TexhFexLabs/HydroNodeStation/doc/presentations/Zusatz.pptx

## Autarke IoT-Wetterstation mit LoRaWAN

Seeed Studio XIAO + SX1262 | Helium IoT | HydroNode
IT6 - DAPI

## Slide 2

HydroStation One

Autarke Umweltüberwachung. Intelligent. Vernetzt. Solarbetrieben.

CO₂-Sensor (SCD41)
Photakustisches Prinzip

XIAO ESP32S3

Wio-SX1262 LoRa

LoRa | WiFi | BLE 5.0

Solar Powered

7 Tage
ohne Sonne

LoRaWAN Reichweite
Bis zu 2 km Reichweite
SF7–SF12 Spreading Factor

Temperatur & Luftfeuchte
BME280 Sensor (Bosch)

Helium IoT Netzwerk
Dezentral & permissionless
Globale LoRaWAN-Abdeckung

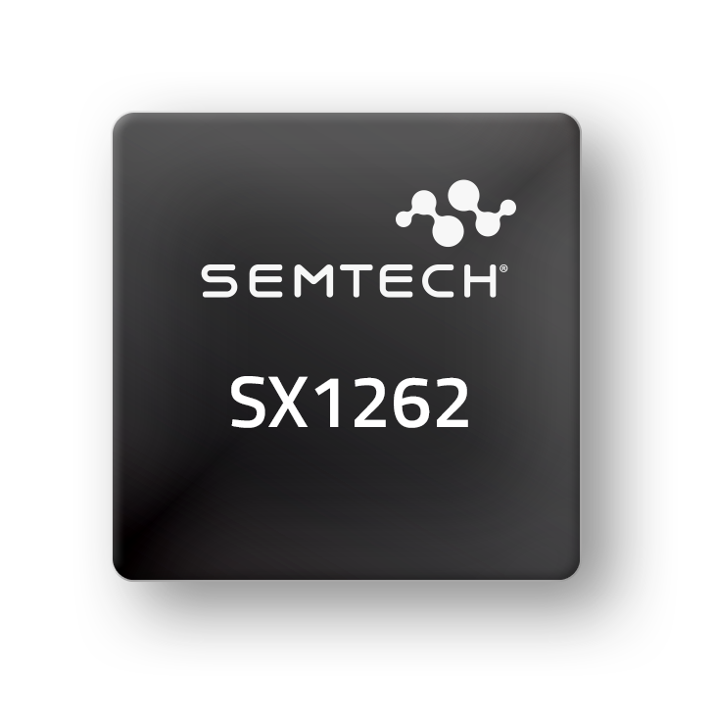
[picture p12: figure]
SX1262

UV-Index Messung
VEML6075
UVA + UVB-Spektrum

7 Tage Autonomie
6W Solarpanel + 2x 3000 mAh LiPo
<2 µA Sleep-Modus

3 Sensoren
integriert

2 km
LoRa Range

1.62 µA
Ultra Low Power

< 100 €
Gesamtsystem

## Slide 3

HydroNode API

Zwei Wege. Eine Plattform. Vollständig abgesichert.

KANAL A

Direkte HTTP-API

IoT-Sensor (ESP32, Arduino)

POST /api/webhook/sensor-value

HMAC-SHA256 Verifikation

Apache Kafka (verified.sensor)

JSON Payload • HTTPS/TLS • ±20 min Replay-Schutz

Header: X-Sensor-Id • X-Timestamp • X-Signature

KANAL B

LoRaWAN / Amazon SNS

LoRaWAN-Sensor

Helium Network / ChirpStack

Amazon SNS (HTTPS)

Apache Kafka (verified.sensor)

Binär-Payload • AES-128 • LoRa Frame Counter

Secret-Hash (SHA-256) • Auto-Subscription

VERARBEITUNG

PostgreSQL
Messwerte speichern

Baseline
72h Rolling Window

Anomalie-Erkennung
Spike • Drop • Drift

GPT-4 Analyse
Alle 60 Minuten
