TexhFexLabs/HydroNodeStation/hardware/schematics_pcb/PCB_PCB2_2026-06-19.pdf

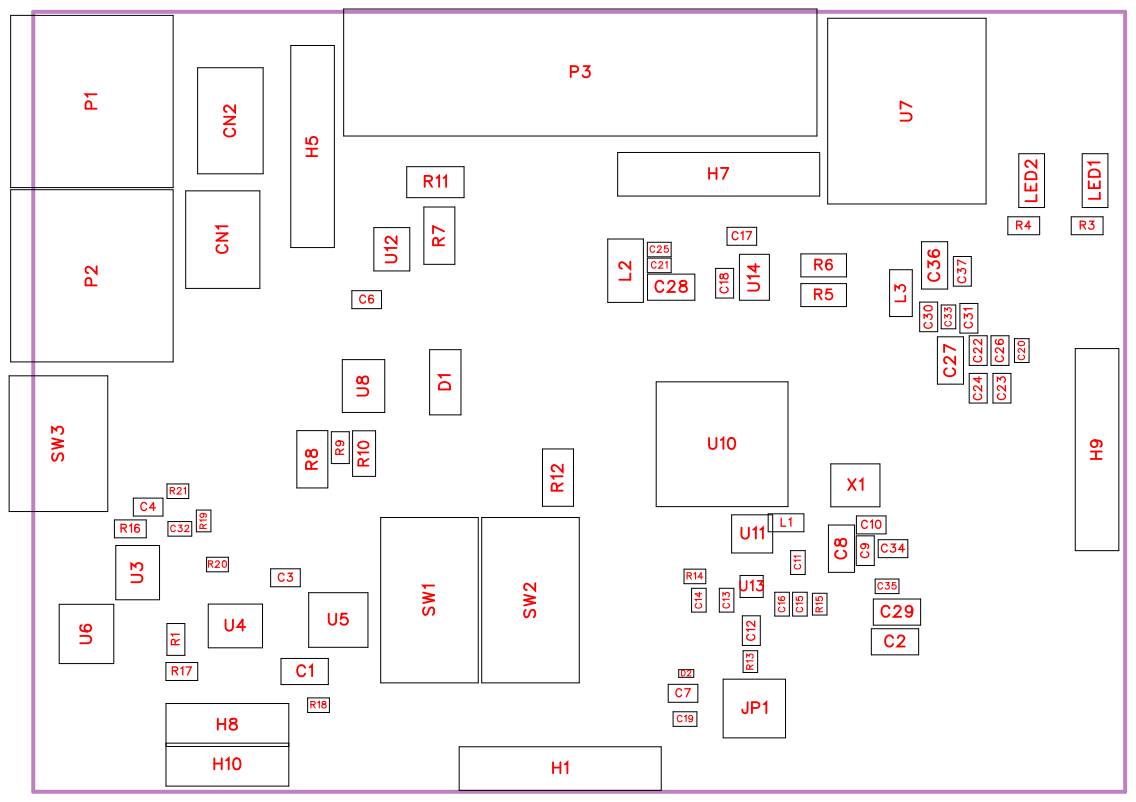
[picture p13: page 1]

No. | Quantity | Comment | Designator | Footprint | Value | Manufacturer Part | Manufacturer | Supplier Part | Supplier | Pin Count | Category
1 | 2 | 22uF | C1,C2 | C0603 | 22uF | CL10A226M Q8NRNC | SAMSUNG( ) 三星 | C59461 | LCSC | 2 | Capacitors:M ultilayer Ceramic Capacitors MLCC -SMD/SMT
2 | 2 | 10uF | C3,C4 | C0402 | 10uF | CL05A106M Q5NUNC | SAMSUNG( 三星 ) | C15525 | LCSC | 2 | Capacitors:M ultilayer Ceramic Capacitors MLCC -SMD/SMT
3 | 10 | 100nF | C6,C7,C22,C23,C24,C26,C 30,C31,C34,C37 | C0402 | 100nF | CC0402KRX 7R7BB104 | YAGEO(国巨 ) | C60474 | LCSC | 2 | Capacitors:M ultilayer Ceramic Capacitors MLCC -SMD/SMT
4 | 1 | 100pF | C8 | C0603 | 100pF | CC0603JRN PO9BN101 | YAGEO(国巨 ) | C14665 | LCSC | 2 | Capacitors:M ultilayer Ceramic Capacitors MLCC -SMD/SMT
5 | 2 | 68pF | C9,C12 | C0402 | 68pF | GCM1555C1 H680JA16D | muRata(村田 ) | C161156 | LCSC | 2 | Capacitors:M ultilayer Ceramic Capacitors MLCC -SMD/SMT
6 | 1 | 47nF | C10 | C0402 | 47nF | GCM155R71 E473KA55D | muRata(村田 ) | C126529 | LCSC | 2 | Capacitors:M ultilayer Ceramic Capacitors MLCC -SMD/SMT
7 | 1 | 68pF | C11 | C0201 | 68pF | GRM0335C1 H680JA01D | muRata(村田 ) | C88914 | LCSC | 2 | Capacitors:M ultilayer Ceramic Capacitors MLCC -SMD/SMT
8 | 3 | 100nF | C13,C15,C19 | C0201 | 100nF | GRM033R61 A104KE15D | muRata(村田 ) | C76934 | LCSC | 2 | Capacitors:M ultilayer Ceramic Capacitors MLCC -SMD/SMT
9 | 2 | 1nF | C14,C16 | C0201 | 1nF | GRM033R71 H102KA12D | muRata(村田 ) | C85934 | LCSC | 2 | Capacitors:M ultilayer Ceramic Capacitors MLCC -SMD/SMT

10 | 2 | 6.8pF | C17,C18 | C0402 | 6.8pF | GJM1555C1 H6R8BB01D | muRata(村田 ) | C88896 | LCSC | 2 | Capacitors:M ultilayer Ceramic Capacitors MLCC -SMD/SMT
11 | 3 | 33pF | C20,C21,C25 | C0201 | 33pF | GJM0335C1 E330GB01D | muRata(村田 ) | C2896796 | LCSC | 2 | Capacitors:M ultilayer Ceramic Capacitors MLCC -SMD/SMT
12 | 3 | 4.7uF | C27,C29,C36 | C0603 | 4.7uF | CC0603KRX 5R7BB475 | YAGEO(国巨 ) | C277476 | LCSC | 2 | Capacitors:M ultilayer Ceramic Capacitors MLCC -SMD/SMT
13 | 1 | 470nF | C28 | C0603 | 470nF | CC0603KRX 5R8BB474 | YAGEO(国巨 ) | C106850 | LCSC | 2 | Capacitors:M ultilayer Ceramic Capacitors MLCC -SMD/SMT
14 | 3 | 100nF | C32,C33,C35 | C0201 | 100nF | C0603X5R1 C104KT00N E | TDK | C694145 | LCSC | 2 | Capacitors:M ultilayer Ceramic Capacitors MLCC -SMD/SMT
15 | 1 | B2B-PH-K-S( LF)(SN) | CN1 | CONN-TH_B 2B-PH-K-S | | B2B-PH-K-S( LF)(SN) | JST | C131337 | LCSC | 2 | Connectors: Wire To Board Connector
16 | 1 | BM04B-SRS S-TB(LF)(SN ) | CN2 | CONN-SMD_ BM04B-SRS S-TB | | BM04B-SRS S-TB(LF)(SN ) | JST | C160390 | LCSC | 6 | Connectors: Wire To Board Connector
17 | 1 | MBRX120LF-TP | D1 | SOD-123_L2 .7-W1.6-LS3. 7-RD | | MBRX120LF-TP | MCC(美微科 ) | C668956 | LCSC | 2 | Diodes:Schot tky Diodes
18 | 1 | ESDALC6V1 -1U2 | D2 | DFN0603-D_ L0.6-W0.3-P 0.34-RD | | ESDALC6V1 -1U2 | ST(意法半导 体) | C1974498 | LCSC | 2 | Circuit Protec tion:ESD and Surge Protection (TVS/ESD)
19 | 4 | PZ254V-11-0 5P | H1,H5,H7,H9 | HDR-TH_5P-P2.54-V-M | | PZ254V-11-0 5P | XFCN(兴飞 ) | C492404 | LCSC | 5 | Connectors:P in Headers
20 | 2 | PZ254V-11-0 3P | H8,H10 | HDR-TH_3P-P2.54-V-M_P Z254V-11-03 P | | PZ254V-11-0 3P | XFCN(兴飞 ) | C2937625 | LCSC | 3 | Connectors:P in Headers

21 | 1 | 6GHz | JP1 | RF-SMD_FR F05002-JSS 103M | 6GHz | U.FL-R-SMT-1(80) | HRS(广濑 ) | C88374 | LCSC | 3 | Connectors: Coaxial Connectors (RF)
22 | 1 | 47nH | L1 | L0402 | 47nH | LQW15AN47 NG00D | muRata(村田 ) | C22334 | LCSC | 2 | Inductors, Coils, Choke s:Power Inductors
23 | 1 | 15uH | L2 | L0805 | 15uH | MLZ2012M1 50WTD25 | TDK | C404760 | LCSC | 2 | Inductors, Coils, Choke s:Inductors (SMD)
24 | 1 | FCM1608KF-601T03 | L3 | L0603 | | FCM1608KF-601T03 | TAI-TECH( 台 庆 ) | C141723 | LCSC | 2 | Filters:Ferrite Beads
25 | 2 | YLED0603R | LED1,LED2 | LED0603-FD | | YLED0603R | YONGYUTAI (永裕泰) | C19171390 | LCSC | 2 | Optoelectroni cs:LED Indication -Discrete
26 | 2 | WJ500V-5.08 -2P | P1,P2 | CONN-TH_2 P-P5.00_WJ 500V-5.08-2 P | | WJ500V-5.08 -2P | KANGNEX( 康奈克斯电气 ) | C8465 | LCSC | 2 | Connectors:S crew Terminal Blocks
27 | 1 | WJ126V-5.0-6P | P3 | CONN-TH_6 P-P5.00_WJ 126V-5.0-6P | | WJ126V-5.0-6P | KANGNEX( 康奈克斯电气 ) | C8379 | LCSC | 6 | Connectors:S crew Terminal Blocks
28 | 2 | 36.5k | R1,R16 | R0402 | 36.5k | 0402WGF36 52TCE | UNI-ROYAL( 厚声 ) | C25887 | LCSC | 2 | Resistors:Chi p Resistor -Surface Mount
29 | 2 | 1k | R3,R4 | R0402 | 1k | FRC0402J10 2 TS | FOJAN(富捷 ) | C2906899 | LCSC | 2 | Resistors:Chi p Resistor -Surface Mount
30 | 2 | 4.7k | R5,R6 | R0603 | 4.7k | 0603WAF47 01T5E | UNI-ROYAL( 厚声 ) | C23162 | LCSC | 2 | Resistors:Chi p Resistor -Surface Mount
31 | 4 | 10k | R7,R8,R11,R12 | R0805 | 10k | FRC0805J10 3TS | FOJAN(富捷 ) | C2930231 | LCSC | 2 | Resistors:Chi p Resistor -Surface Mount
32 | 1 | 12k | R9 | R0402 | 12k | 0402WGF12 02TCE | UNI-ROYAL( 厚声 ) | C25752 | LCSC | 2 | Resistors:Chi p Resistor -Surface Mount
33 | 1 | 300 | R10 | R0603 | 300 | FRC0603J30 1 TS | FOJAN(富捷 ) | C2907148 | LCSC | 2 | Resistors:Chi p Resistor -Surface Mount
34 | 5 | 0 | R13,R18,R19,R20,R21 | R0201 | 0 | CRCW02010 000Z0ED | VISHAY(威世 ) | C844709 | LCSC | 2 | Resistors:Chi p Resistor -Surface Mount

35 | 2 | 100 | R14,R15 | R0201 | 100 | CRCW02011 00RFNED | VISHAY(威世 ) | C2073844 | LCSC | 2 | Resistors:Chi p Resistor -Surface Mount
36 | 1 | 8.25k | R17 | R0402 | 8.25k | FRC0402F82 51TS | FOJAN(富捷 ) | C5126132 | LCSC | 2 | Resistors:Chi p Resistor -Surface Mount
37 | 2 | TS-1095PS-A1B2-C3D2 | SW1,SW2 | KEY-SMD_4 P-L6.0-W6.0-P3.90-LS9.0 | | TS-1095PS-A1B2-C3D2 | Yuandi(元迪 ) | C2834918 | LCSC | 4 | Switches:Tac tile Switches
38 | 1 | MK-12C02-G 020 | SW3 | SW-SMD_M K-12C02-G0 20 | | MK-12C02-G 020 | G-Switch( 品 赞 ) | C963206 | LCSC | 7 | Switches:Slid e Switches
39 | 2 | TPS63900D SKR | U3,U4 | WSON-10_L 2.5-W2.5-W0 .50-TL-EP | | TPS63900D SKR | TI(德州仪器 ) | C1518762 | LCSC | 11 | Power Management (PMIC):DC-D C Converters
40 | 2 | 2.2uH | U5,U6 | IND-SMD_L3 .0-W3.0_LVF 303012-4R7 M-N | 2.2uH | SRN3015-2R 2M | BOURNS | C2041716 | LCSC | 2 | Inductors, Coils, Choke s:Power Inductors
41 | 1 | SMQS-04R-T P | U7 | SW-TH_8P-P 2.54_SMQS-04R-TP | | SMQS-04R-T P | SM Switch | C5299505 | LCSC | 8 | Switches:DIP Switches
42 | 1 | BQ25185DL HR | U8 | WSON-10_L 2.2-W2.0-P0. 40-BL-EP_TI _DLH0010A | | BQ25185DL HR | TI(德州仪器 ) | C19725033 | LCSC | 11 | Power Management (PMIC):Batte ry Management
43 | 1 | STM32WLE5 CCU6 | U10 | UFQFPN-48 _L7.0-W7.0-P0.50-BL-EP 5.6 | | STM32WLE5 CCU6 | ST(意法半导 体) | C2888218 | LCSC | 49 | Embedded Processors & Controllers:M icrocontroller s (MCU/MPU /SOC)
44 | 1 | BALFHB-WL-02D3 | U11 | CSPG-8_L2. 1-W1.8_BAL FHB-WL-03D 3 | | BALFHB-WL-02D3 | ST(意法半导 体) | C5350082 | LCSC | 8 | RF and Wireless:RF Filters
45 | 1 | MAX17048G +T10 | U12 | TDFN-8_L2.0 -W2.0-P0.50-BL-EP1.2 | | MAX17048G +T10 | ADI(亚德诺)/ MAXIM(美信 ) | C2682616 | LCSC | 9 | Power Management (PMIC):Batte ry Management
46 | 1 | BGS12SN6E 6327XTSA1 | U13 | TSNP-6_L1.1 -W0.7-P0.40-BL | | BGS12SN6E 6327XTSA1 | Infineon(英飞 凌) | C114953 | LCSC | 6 | RF and Wireless:RF Switches
47 | 1 | 32.768kHz | U14 | CRYSTAL-S MD_L2.0-W1 .2 | 32.768kHz | NX2012SA-3 2.768KHZ-E XS00A-MU0 0527 | NDK | C7016235 | LCSC | 2 | Crystals, Oscillators, R esonators:Cr ystals

48

1 | 32MHz | X1 | CRYSTAL-S MD_4P-L2.0- W1.6-BL
32MHz | NX2016SA-3
2M-EXS00A-CS06465
NDK | C1986260 | LCSC
4 | Crystals,
Oscillators, R
esonators:Cr
ystals

Add into BOM | Convert to PCB | 3D Model Title | Device | Name
yes | | C0603_L1.6-W0.8-H0.8 | CL10A226M Q8NRNC | 22uF
yes | | C0402_L1.0-W0.5-H0.5 | CL05A106M Q5NUNC | 10uF
yes | | C0402_L1.0-W0.5-H0.5 | CC0402KRX 7R7BB104 | 100nF
yes | | C0603_L1.6-W0.8-H0.8 | CC0603JRN PO9BN101 | 100pF
yes | | C0402_L1.0-W0.5-H0.5 | GCM1555C1 H680JA16D | 68pF
yes | | C0402_L1.0-W0.5-H0.5 | GCM155R71 E473KA55D | 47nF
yes | | C0201_L0.6-W0.3-H0.3 | GRM0335C1 H680JA01D | 68pF
yes | | C0201_L0.6-W0.3-H0.3 | GRM033R61 A104KE15D | 100nF
yes | | C0201_L0.6-W0.3-H0.3 | GRM033R71 H102KA12D | 1nF
yes | | C0402_L1.0-W0.5-H0.5 | GJM1555C1 H6R8BB01D | 6.8pF
yes | | C0201_L0.6-W0.3-H0.3 | GJM0335C1 E330GB01D | 33pF
yes | | C0603_L1.6-W0.8-H0.8 | CC0603KRX 5R7BB475 | 4.7uF
yes | | C0603_L1.6-W0.8-H0.8 | CC0603KRX 5R8BB474 | 470nF
yes | | C0201_L0.6-W0.3-H0.3 | C0603X5R1 C104KT00N E | 100nF
yes | | CONN-TH_P H2.00-LI-2P | B2B-PH-K-S( LF)(SN) | B2B-PH-K-S( LF)(SN)
yes | | CONN-SMD_ 4P-L6.0-W2. 9-H4.3-P1.0 | BM04B-SRS S-TB(LF)(SN ) | BM04B-SRS S-TB(LF)(SN )
yes | | SOD-123_L2 .7-W1.6-H1.4 -LS3.7 | MBRX120LF-TP | MBRX120LF-TP
yes | | DFN0603-D_ L0.6-W0.3-H 0.3 | ESDALC6V1 -1U2 | ESDALC6V1 -1U2
yes | | HDR-TH_5P-P2.54-M-LI-1 X5P | PZ254V-11-0 5P | PZ254V-11-0 5P
yes | | HDR-TH_3P-P2.54-V-M_P Z254V-11-03 P | PZ254V-11-0 3P | PZ254V-11-0 3P

yes | RF-SMD_FR F05002-JSS 103M | U.FL-R-SMT-1(80)_C8837 4 | 6GHz
yes | L0402_L1.0-W0.5-H0.5_B EAD | LQW15AN47 NG00D | 47nH
yes | R0805_L2.0-W1.3-H0.6 | MLZ2012M1 50WTD25 | 15uH
yes | L0603_L1.6-W0.8-H0.5_B EAD | FCM1608KF-601T03 | FCM1608KF-601T03
yes | LED0603_Inf | YLED0603R | YLED0603R
yes | CONN-TH_2 P-P5.00_WJ 500V-5.08-2 P | WJ500V-5.08 -2P | WJ500V-5.08 -2P
yes | CONN-TH_6 P-P5.00_WJ 126V-5.0-6P | WJ126V-5.0-6P | WJ126V-5.0-6P
yes | R0402_L1.0-W0.5-H0.4 | 0402WGF36 52TCE | 36.5k
yes | R0402_L1.0-W0.5-H0.4 | FRC0402J10 2 TS | 1k
yes | R0603 | 0603WAF47 01T5E | 4.7k
yes | R0805_L2.0-W1.3-H0.6 | FRC0805J10 3TS | 10k
yes | R0402_L1.0-W0.5-H0.4 | 0402WGF12 02TCE | 12k
yes | R0603 | FRC0603J30 1 TS | 300
yes | R0201_L0.6-W0.3-H0.3 | CRCW02010 000Z0ED | 0
yes | R0201_L0.6-W0.3-H0.3 | CRCW02011 00RFNED | 100
yes | R0402_L1.0-W0.5-H0.4 | FRC0402F82 51TS | 8.25k
yes | KEY-SMD_4 P-L6.0-W6.0-H8.0-P3.90-L S9.0 | TS-1095PS-A1B2-C3D2 | TS-1095PS-A1B2-C3D2
yes | SW-SMD_M K-12C02-G0 20 | MK-12C02-G 020 | MK-12C02-G 020
yes | WSON-10_L 2.5-W2.5-W0 .50-TL-EP | TPS63900D SKR | TPS63900D SKR
yes | | SRN3015-2R 2M | 2.2uH

yes | SW-TH_8P-P 2.54_SMQS-04R-TP | SMQS-04R-T P | SMQS-04R-T P
yes | WSON-10_L 2.2-W2.0-P0. 40-BL-EP_TI _DLH0010A | BQ25185DL HR | BQ25185DL HR
yes | UFQFPN-48 _L7.0-W7.0-H0.6-P0.50 | STM32WLE5 CCU6 | STM32WLE5 CCU6
yes | CSPG-8_L2. 1-W1.8_BAL FHB-WL-03D 3 | BALFHB-WL-02D3 | BALFHB-WL-02D3
yes | TDFN-8_L2.0 -W2.0-P0.50-BL-EP1.2 | MAX17048G +T10 | MAX17048G +T10
yes | TSNP-6_L1.1 -W0.7-H0.4-P0.40-BL | BGS12SN6E 6327XTSA1 | BGS12SN6E 6327XTSA1
yes | CRYSTAL-S MD_L2.0-W1 .2 | NX2012SA-3 2.768KHZ-E XS00A-MU0 0527 | 32.768kHz
yes | CRYSTAL-S MD_4P-L2.0-W1.6-BL | NX2016SA-3 2M-EXS00A-CS06465 | 32MHz

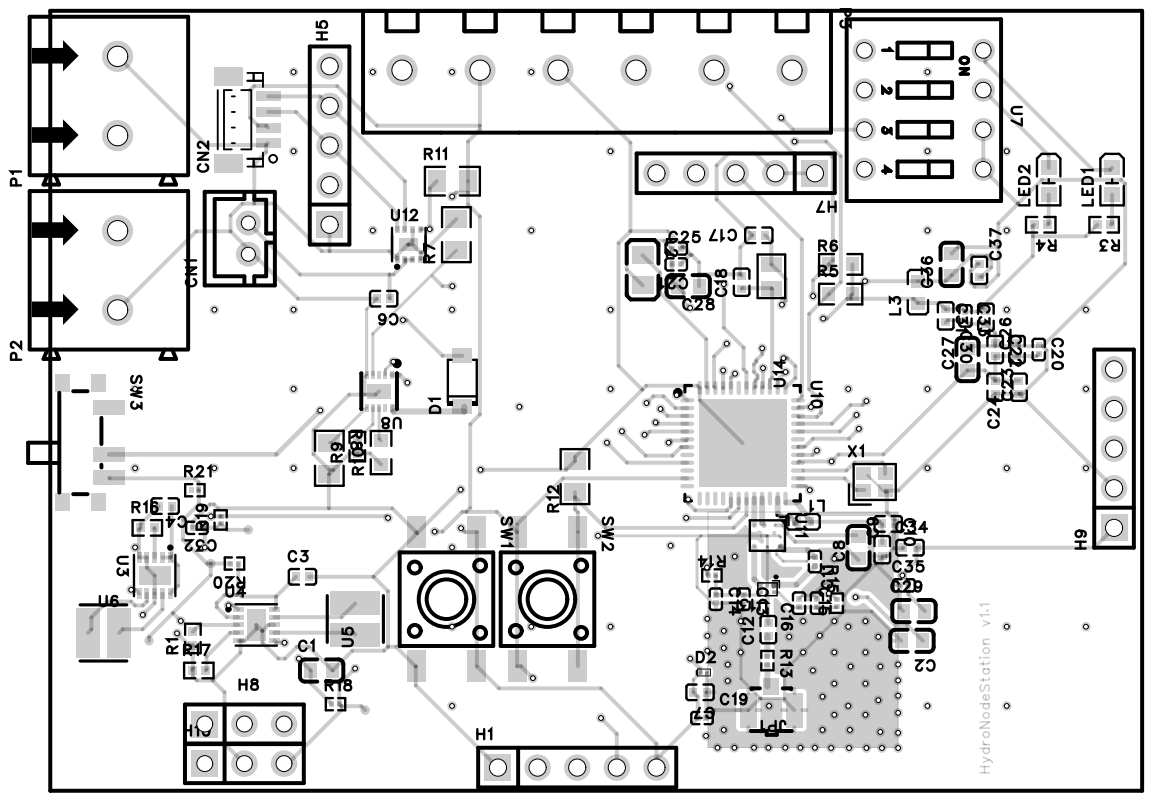
[picture p14: page 11]

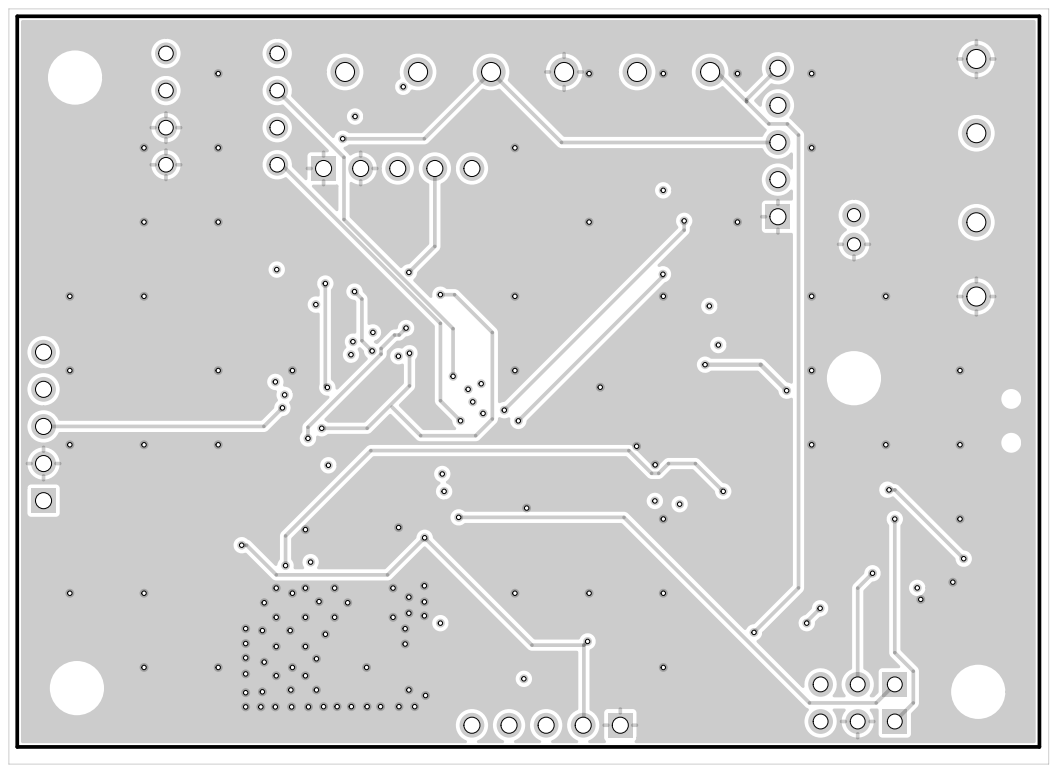
[picture p15: page 12]

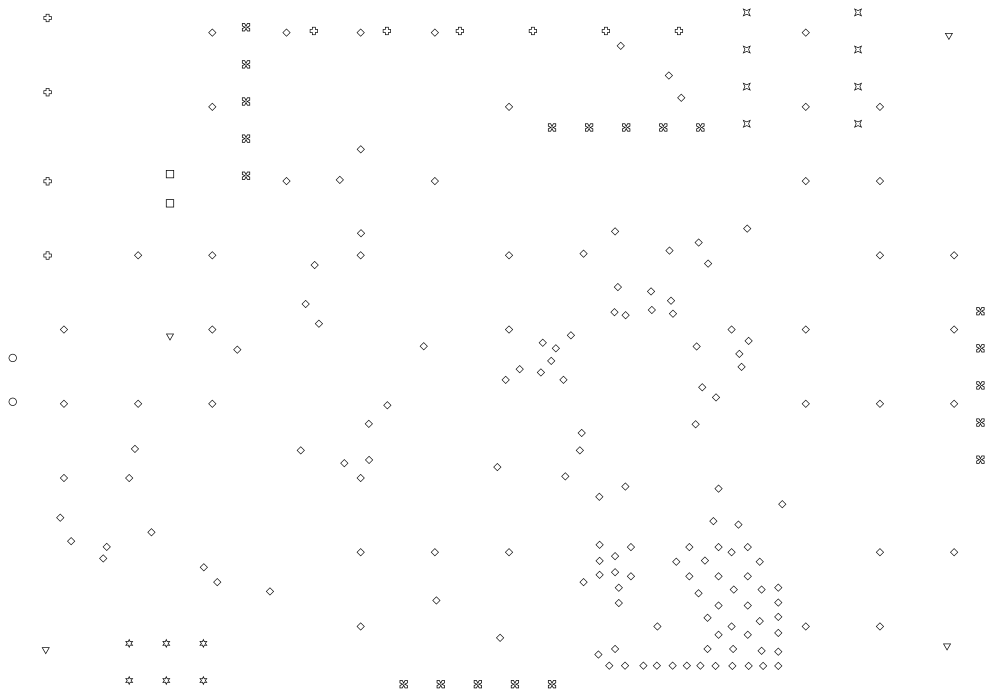
[picture p16: page 13]

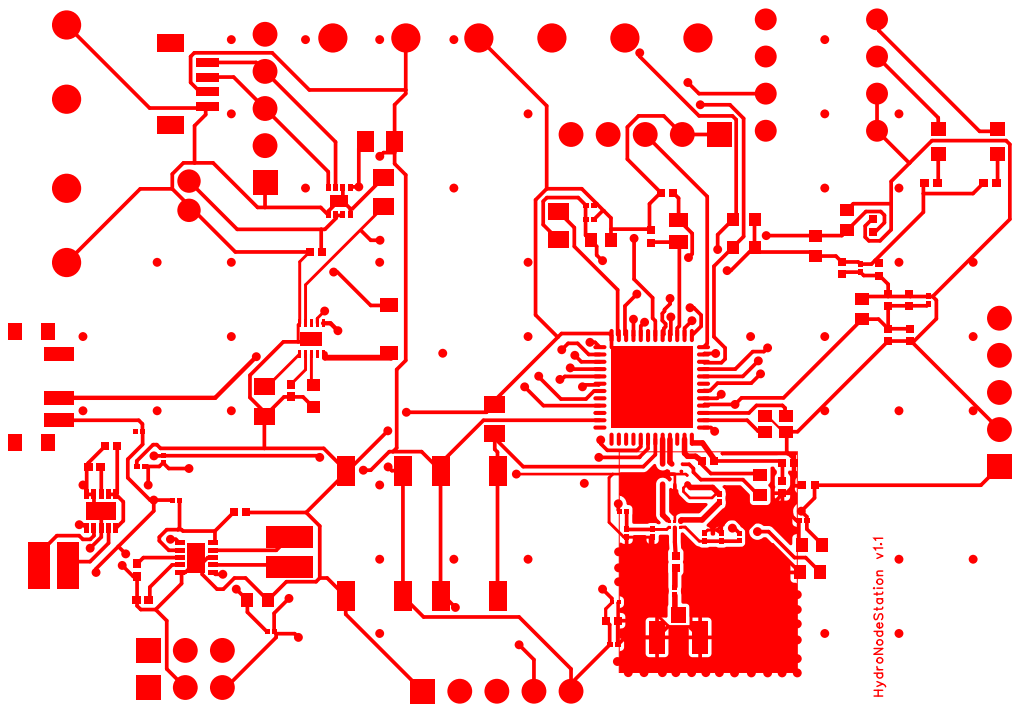
[picture p17: page 14]

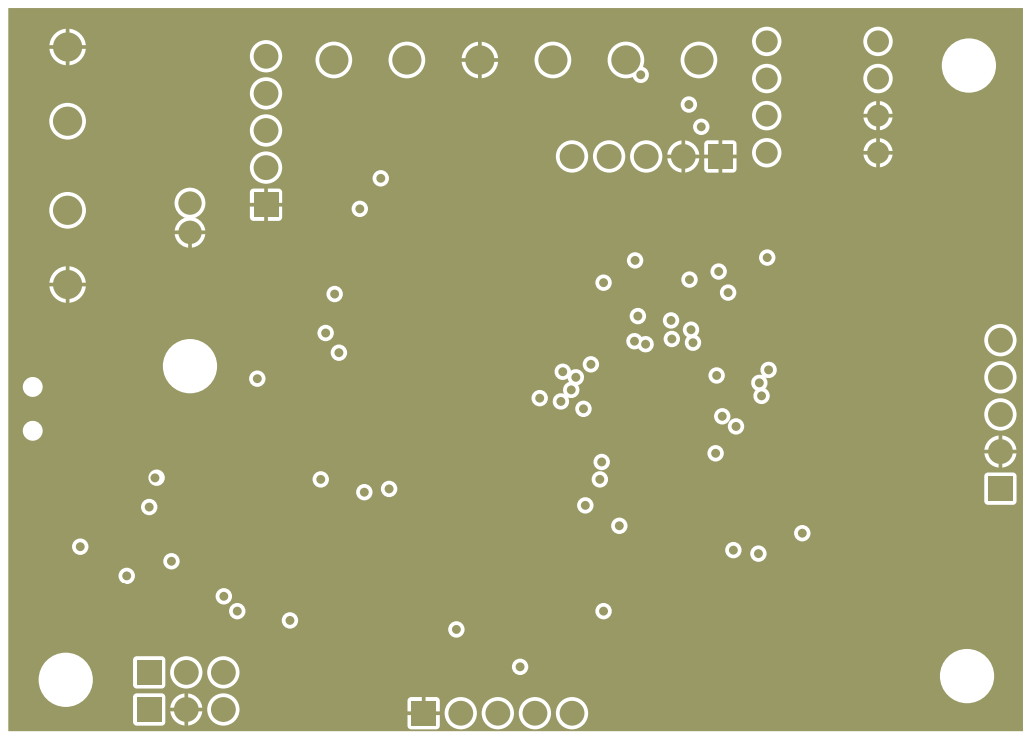
[picture p18: page 15]

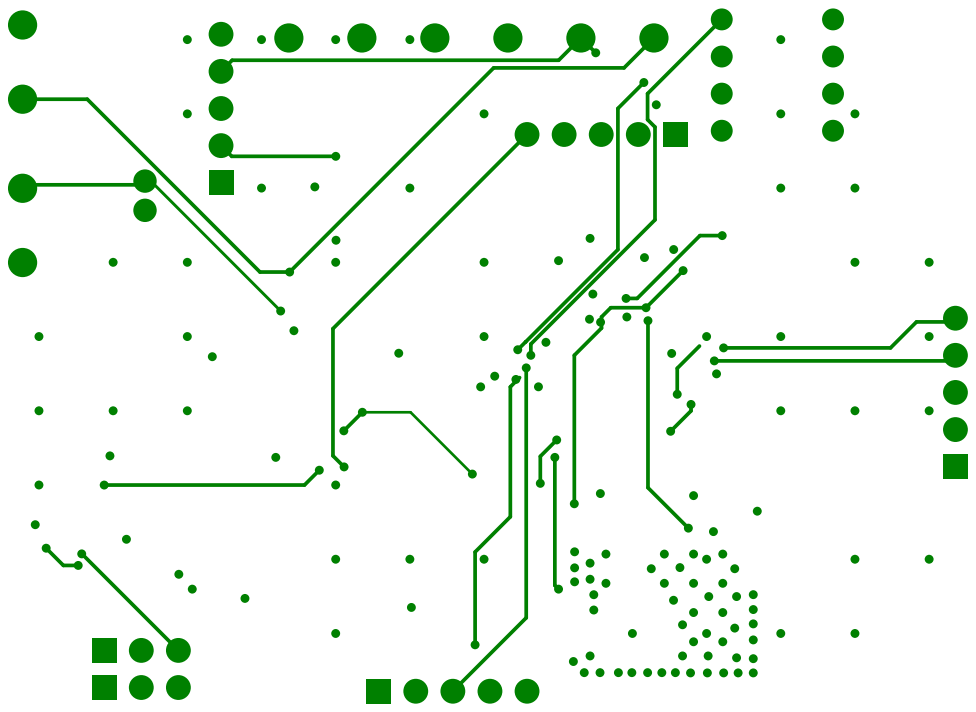
[picture p19: page 16]

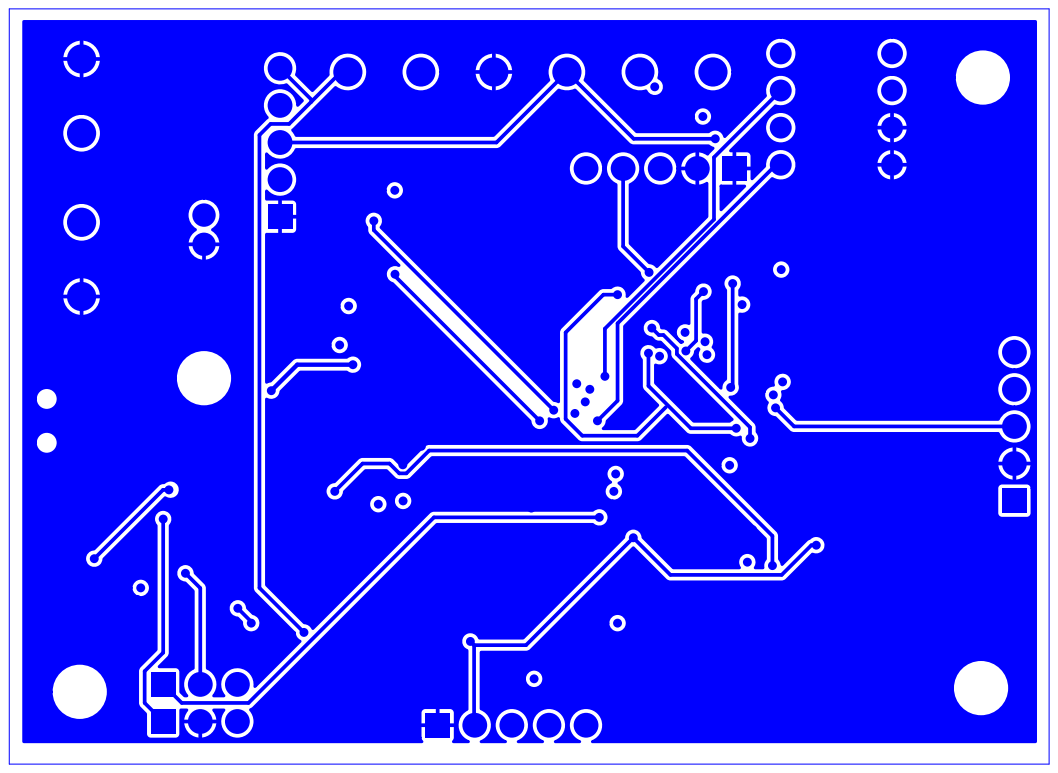
[picture p20: page 17]

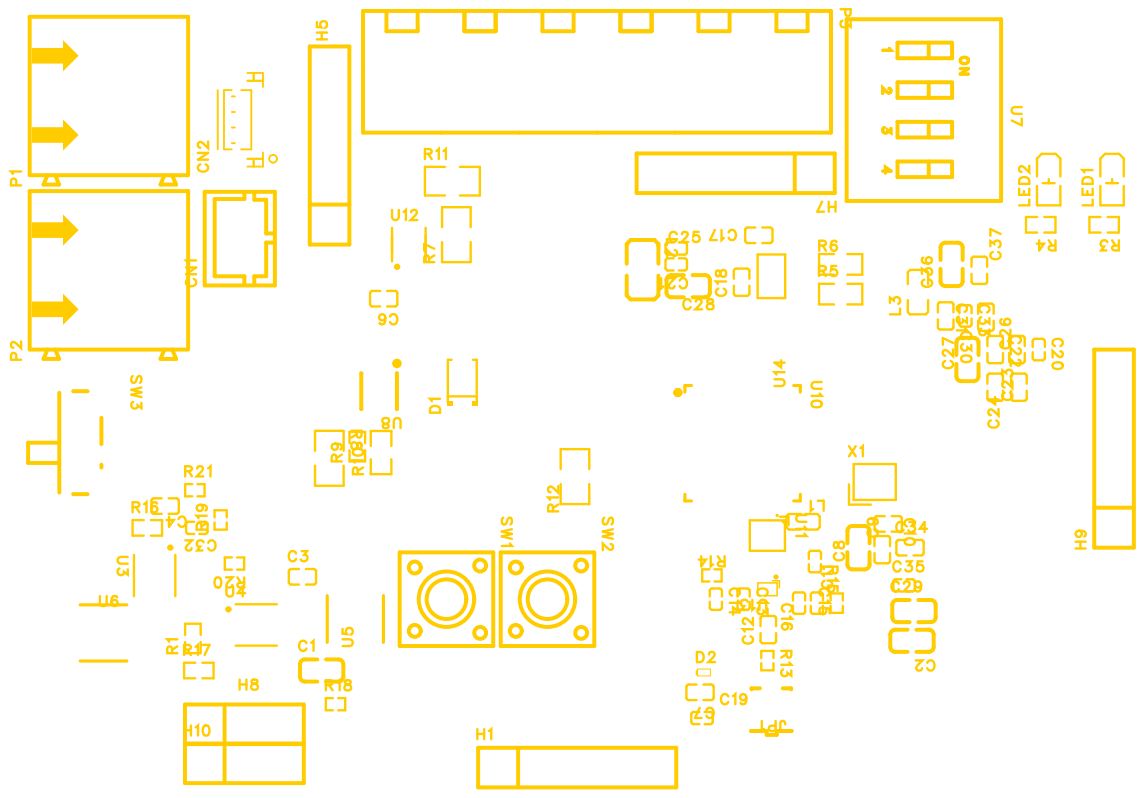
[picture p21: page 18]
