TexhFexLabs/HydroNodeStation/doc/kurzuebersicht/hydronode-kurzuebersicht.pdf

## Umweltmessstation HydroNodeStation01

Kurzübersicht

Felix Knoll | · OTH Regensburg | · 6. September 2026

## Kurzfassung

Die HydroNodeStation01 ist eine solarbetriebene Umweltmessstation für den autonomen Außeneinsatz. Sie misst Temperatur, Luftfeuchte, Luftdruck, UV-Index, CO2 und Feinstaub und überträgt die Werte per LoRaWAN an ein öffentliches Dashboard. Sie benötigt weder einen Stromanschluss noch einen Netzwerkanschluss und läuft seit Ende Mai 2026 im Freien.
Die Station entstand als Projektarbeit im Studiengang Technische Informatik. Platine, Gehäuse, Firmware und Backend wurden vollständig neu entwickelt, weil für den verwendeten Funkchip kein geeignetes offenes Design verfügbar war.
Punkt | Angabe
Messintervall | 3 Minuten. CO2 alle 15 Minuten, Feinstaub alle 30 Minuten
Energieversorgung | Solarpanel mit Pufferakku
Übertragung | LoRaWAN über das Helium-Netz
Reichweite | Im Feldtest über 10 Kilometer nachgewiesen
Materialkosten | rund 250 Euro je Station
Entwicklungsaufwand | 170 Stunden
Lizenz | Hardware CC BY-NC-SA 4.0, Firmware BSD-3-Clause
Stand | Im Feldtest seit Ende Mai 2026

## Messgrößen

Sensor | Messgröße | Genauigkeit
SHT45 | Temperatur, Luftfeuchte | ◦C, ±1,0 % ±0,1
BMP390 | Luftdruck | ±0,5 hPa
LTR390 | UV-Index
SCD41 | CO2 | ±40 ppm
SPS30 | Feinstaub PM1.0, PM2.5, PM4.0, PM10
MAX17048 | Akkuspannung der Station

Die Sensoren sitzen in einem selbst konstruierten Lamellengehäuse nach dem Prinzip der Wetterhütte, gedruckt aus weißem ASA. Das Material ist UV-beständig und witterungsfest. Das Gehäuse hält Direktsonne und Regen von den Sensoren fern und lässt gleichzeitig Luft zirkulieren.

## Betrieb

Gemessen wurde ein mittlerer Stromverbrauch von rund 2,12 Milliampere, entsprechend etwa 50,9 Milliamperestunden pro Tag. Mit einem Akku von 1200 Milliamperestunden ergibt das eine Reserve von rund 24 Tagen ohne Sonneneinstrahlung.
Fällt die Akkuspannung unter 3300 Millivolt, schaltet die Station Funk und Sensoren ab und prüft nur noch minütlich die Versorgung. Sie nimmt den Messbetrieb selbsttätig wieder auf, sobald

1

die Spannung 3600 Millivolt erreicht und diese Schwelle eine Minute lang hält. Zwischen 3500 und 3650 Millivolt sendet sie im doppelten Intervall. Eine Station, die zeitweise schweigt, ist deshalb nicht zwingend defekt.
Die Firmware überwacht sich selbst und startet im Störungsfall neu. Sie meldet sich anschließend ohne Eingriff von außen wieder am Funknetz an.
Zum Aufstellen wird ein Platz im Freien mit ausreichender Sonneneinstrahlung für das Solarpanel benötigt. Weitere Infrastruktur ist nicht erforderlich.

## Kosten und Aufwand

Position | Betrag
Elektronik mit allen sechs Sensoren | 150 bis 200 Euro
ASA-Filament für das Gehäuse | rund 30 Euro
3D-Druck, Solarpanel, Akku und Kleinteile | übrige Kosten
Gesamt je Station | rund 250 Euro

Angegeben sind Materialkosten ohne Arbeitszeit. Die Platinen mussten im Fünferpack bestellt werden, weil der Fertiger keine kleineren Mengen anbietet. Fünf Stück kosteten inklusive Versand rund 200 Euro. Beschränkt man die Bestückung auf Temperatur, Feuchte, Druck und UV und verzichtet auf CO2 und Feinstaub, sinken die Kosten der Elektronik auf unter 30 Euro.
Der Entwicklungsaufwand lag bei 170 Stunden gegenüber 160 geplanten. Der größte Mehraufwand entfiel auf den Platinenentwurf mit rund 50 statt der geplanten 9 Stunden sowie auf das Gehäuse mit rund 12 Stunden, das ursprünglich nicht eingeplant war.

## Daten und Veröffentlichung

Die Messwerte laufen über das Funknetz in HydroNode, eine selbst entwickelte Plattform aus Backend, Weboberfläche und iOS-App. Eine automatische Anomalieerkennung prüft die Messreihen und meldet auffällige Sprünge oder Ausfälle. Die Plattform ist über diese eine Station hinaus einsetzbar.
Die Live-Werte der Station sind öffentlich und ohne Benutzerkonto einsehbar:

https://hydronode.tech/stations/public/004dd7e7-5c27-4de0-bff5-24116f721658

Geplant ist, mehrere Stationen dieser Bauart an verschiedenen Standorten aufzustellen, damit möglichst viele Menschen Messwerte aus ihrer unmittelbaren Umgebung einsehen können.
Das Projekt ist quelloffen veröffentlicht. Schaltplan, Platinenentwurf, Gehäusedaten, Stückliste, Firmware und Inbetriebnahmeanleitung liegen unter https://github.com/TexhFexLabs/hydro NodeStation01. (https://github.com/TexhFexLabs/hydroNodeStation01) Hardware und Gehäuse stehen unter CC BY-NC-SA 4.0, die Firmware unter BSD-3-Clause.

## Stand und offene Punkte

Alle sechs Sensoren, der LoRaWAN-Betrieb und die Übertragung ins Backend sind verifiziert. Die Station steht seit Ende Mai 2026 im Außentest.
Zwei Punkte sind noch offen. Die Solarautarkie unter verschiedenen Lichtbedingungen ist nicht abschließend verifiziert, und die Langzeitmessung der tatsächlichen Batterielaufzeit läuft noch. Die ausführliche technische Dokumentation liegt als Projektdokumentation zur HydroNodeStation01 bei.

2
