TexhFexLabs/HydroNodeStation/stm32_node/LoRaWAN/App/lora_app.c

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

/* Includes ------------------------------------------------------------------*/
#include "platform.h"
#include "sys_app.h"
#include "lora_app.h"
#include "stm32_seq.h"
#include "stm32_timer.h"
#include "utilities_def.h"
#include "app_version.h"
#include "Commissioning.h"
#include "subghz_phy_version.h"
#include "smtc_modem_api.h"
#include "smtc_modem_utilities.h"
#include "smtc_modem_hal.h"
#include "smtc_modem_relay_api.h"
#include "adc_if.h"
#include "sys_sensors.h"
#include "rng.h"
#include "lorawan_api.h"
#include "sps30.h"
#include "stm32_lpm.h"

/* USER CODE BEGIN Includes */
#include "bq25185.h"
#include "power_policy.h"
#include "runtime_health.h"
#include "max17048.h"
#include "i2c.h"
#include "nvm_store.h"
#include "link_check.h"
#include "ina226.h"
#include "solar.h"
#include "payload.h"
#include "pulse_counter.h"
#include "fault_report.h"
#include "standby.h"
#include "device_settings.h"
#include "led.h"
/* USER CODE END Includes */

/* External variables ---------------------------------------------------------*/
/**
  * @brief LoRa State Machine states
  */
typedef enum TxEventType_e
{
  /**
    * @brief Appdata Transmission issue based on timer every TxDutyCycleTime
    */
  TX_ON_TIMER,
  /**
    * @brief Appdata Transmission external event plugged on OnSendEvent( )
    */
  TX_ON_EVENT
} TxEventType_t;

/* USER CODE BEGIN PTD */
/**
  * @brief Persistent application configuration layout (8 bytes, flash-stored).
  */
typedef struct
{
  uint32_t magic;
  uint32_t tx_dutycycle_s;
} app_config_t;

/**
  * @brief Config area in the NVM snapshot: the 2.0 interval record, kept so a
  *        downgrade still finds its interval, then the 2.1 device settings
  *        (device_settings.h). Both go to flash in one write.
  */
typedef struct
{
  app_config_t legacy;
  uint8_t settings[SETTINGS_RECORD_LEN];
} app_store_t;
_Static_assert(NVM_CONFIG_OFFSET + sizeof(app_store_t) <= NVM_PAYLOAD_BYTES,
               "config area must fit the NVM payload");
/* USER CODE END PTD */

/**
  * LEDs period value of the timer in ms
  */
#define LED_PERIOD_TIME 500

/**
  * Join switch period value of the timer in ms
  */
#define JOIN_TIME 2000

/**
  * Uplink time interval in Certification mode is 10s (recommended value)
  */
#define CERT_TX_DUTYCYCLE   10

/**
  * Stack id value (multistacks modem is not yet available)
  */
#define STACK_ID 0

/*---------------------------------------------------------------------------*/
/*                             LoRaWAN NVM configuration                     */
/*---------------------------------------------------------------------------*/
/* Legacy context sizes are validated at the NVM adapter boundary. */
#define SECURE_ELEMENT_CONTEXT_SIZE 0x2A0UL
#define MODEM_CONTEXT_SIZE          0x10UL
#define LORAWAN_CONTEXT_SIZE        0x28UL

/* USER CODE BEGIN PD */
/**
  * @brief SPS30 Manual Fan cleaning interval in hours
  */
#define SPS30_FAN_CLEAN_INTERVAL_HOURS  120U

/**
  * @brief RX command port and codes
  */
#define RX_CMD_PORT                      LORAWAN_USER_APP_PORT
#define RX_CMD_TRIGGER_SPS30_CLEANING    0x11U
#define RX_CMD_SET_TX_INTERVAL           0x10U
#define RX_CMD_SOFTWARE_RESET            0xFFU

/**
  * @brief Fault and event frames (TD_2_0_15)
  */
#define TX_PORT_FAULTS                   99U

/**
  * @brief Installation mode (DIP 4, TD_2_0_19)
  */
#define INSTALL_DURATION_S               1800U
#define INSTALL_INTERVAL_S               60U
#define INSTALL_LINKCHECK_EVERY          3U
#define INSTALL_LINKCHECK_MAX            10U   /* TTN fair use: 10 downlinks a day */

/**
  * @brief LED1 start phase (TD_2_0_20): join attempts, join, first uplink
  */
#define LED_START_PHASE_S                1800U


/* Application config shares the transactional NVM snapshots. */
#define APP_CONFIG_MAGIC                 (0x484E4331UL)   /* "HNC1" - HydroNode Config v1 */

/**
  * @brief BQ25185 charger safety-timer reset cadence in ms (independent CE-pulse timer).
  * @note  Must stay well below the charger's internal ~6 h safety timeout.
  */
#define BQ25185_SAFETY_RESET_INTERVAL_MS (2U * 60U * 60U * 1000U)

/* USER CODE END PD */


/*!
 * @brief Stringify constants
 */
#define xstr( a ) str( a )
#define str( a ) #a

/*!
 * @brief Helper macro that returned a human-friendly message if a command does not return SMTC_MODEM_RC_OK
 *
 * @remark The macro is implemented to be used with functions returning a @ref smtc_modem_return_code_t
 *
 * @param[in] rc  Return code
 */

#define ASSERT_SMTC_MODEM_RC( rc_func )                                                     \
  do                                                                                        \
  {                                                                                         \
    smtc_modem_return_code_t rc = rc_func;                                                  \
    if( rc == SMTC_MODEM_RC_NOT_INIT )                                                      \
    {                                                                                       \
      APP_LOG(TS_OFF, VLEVEL_H,  "In %s - %s (line %d): %s\r\n", __FILE__, __func__, __LINE__,   \
              xstr( SMTC_MODEM_RC_NOT_INIT ) );                             \
    }                                                                                       \
    else if( rc == SMTC_MODEM_RC_INVALID )                                                  \
    {                                                                                       \
      APP_LOG(TS_OFF, VLEVEL_H,  "In %s - %s (line %d): %s\r\n", __FILE__, __func__, __LINE__,   \
              xstr( SMTC_MODEM_RC_INVALID ) );                              \
    }                                                                                       \
    else if( rc == SMTC_MODEM_RC_BUSY )                                                     \
    {                                                                                       \
      APP_LOG(TS_OFF, VLEVEL_H,  "In %s - %s (line %d): %s\r\n", __FILE__, __func__, __LINE__,   \
              xstr( SMTC_MODEM_RC_BUSY ) );                                 \
    }                                                                                       \
    else if( rc == SMTC_MODEM_RC_FAIL )                                                     \
    {                                                                                       \
      APP_LOG(TS_OFF, VLEVEL_H,  "In %s - %s (line %d): %s\r\n", __FILE__, __func__, __LINE__,   \
              xstr( SMTC_MODEM_RC_FAIL ) );                                 \
    }                                                                                       \
    else if( rc == SMTC_MODEM_RC_NO_TIME )                                                  \
    {                                                                                       \
      APP_LOG(TS_OFF, VLEVEL_L,  "In %s - %s (line %d): %s\r\n", __FILE__, __func__, __LINE__, \
              xstr( SMTC_MODEM_RC_NO_TIME ) );                            \
    }                                                                                       \
    else if( rc == SMTC_MODEM_RC_INVALID_STACK_ID )                                         \
    {                                                                                       \
      APP_LOG(TS_OFF, VLEVEL_H,  "In %s - %s (line %d): %s\r\n", __FILE__, __func__, __LINE__,   \
              xstr( SMTC_MODEM_RC_INVALID_STACK_ID ) );                     \
    }                                                                                       \
    else if( rc == SMTC_MODEM_RC_NO_EVENT )                                                 \
    {                                                                                       \
      APP_LOG(TS_OFF, VLEVEL_M,  "In %s - %s (line %d): %s\r\n", __FILE__, __func__, __LINE__,    \
              xstr( SMTC_MODEM_RC_NO_EVENT ) );                              \
    }                                                                                       \
  } while( 0 )


/**
  * @brief  LoRa End Node send request
  */
static void SendTxData(uint8_t port);
static void ScheduleNextRound(void);
static void BuildBlock(payload_block_t *block);
static void CommitBlock(const payload_block_t *block);
static void ProcessSensorEvents(void);
static void ServicePower(void);
static void ServiceJoin(void);
static void ReadBattery(void);
static void StopSensorTimers(void);
static void ReportPower(void);
static void ReportNvm(void);
static bool SendFaultFrame(void);
static void processRxData(const uint8_t *payload, uint8_t size, const smtc_modem_dl_metadata_t *metadata);

#if defined (LOW_POWER_DISABLE) && (LOW_POWER_DISABLE == 0)
/**
  * @brief  Sleep timer callback function
  * @param  context ptr
  */
static void OnSleepTimerEvent(void *context);
#endif /* (LOW_POWER_DISABLE) && (LOW_POWER_DISABLE == 0) */

/**
  * @brief User callback for event
  *
  *  This callback is called every time an event ( see smtc_modem_event_t ) appears in the modem.
  *  Several events may have to be read from the modem when this callback is called.
  */
static void EventCallback(void);

/*!
 * Restore the NVM Data context from the Flash
 *
* @param [in]  ctx_type   Type of modem context that need to be restored
* @param [in]  offset     Memory offset after ctx_type address
* @param [out] buffer     Buffer pointer to write to
* @param [in]  size       Buffer size to read in bytes
*/
static void RestoreContext(const modem_context_type_t ctx_type, uint32_t offset, uint8_t *buffer, const uint32_t size);
/*!
 * Store the NVM Data context to the Flash
 *
* @param [in] ctx_type   Type of modem context that need to be saved
* @param [in] offset     Memory offset after ctx_type address
* @param [in] buffer     Buffer pointer to write from
* @param [in] size       Buffer size to write in bytes
*/
static void StoreContext(const modem_context_type_t ctx_type, uint32_t offset, const uint8_t *buffer,
                         const uint32_t size);
/*!
 * Get Random value using the RNG module
 *
 * \retval value  Return the random value
 */
static uint32_t GetRandomValue(void);

/*!
 * Will be called to reset the system
 * \note Compliance test protocol callbacks used when TS001-1.0.4 + TS009 1.0.0 are defined
 */
static void SystemReset(void);

/* USER CODE BEGIN PFP

static bool IsAllZero(const uint8_t *buffer, uint8_t size);
 */
/**
  * @brief  LED Tx timer callback function
  * @param  context ptr of LED context
  
static void OnTxTimerLedEvent(void *context);
*/
/**
  * @brief  LED Rx timer callback function
  * @param  context ptr of LED context
static void OnRxTimerLedEvent(void *context);
 */
/**
  * @brief  LED Join timer callback function
  * @param  context ptr of LED context
  
static void OnJoinTimerLedEvent(void *context);
*/
/**
  * @brief  SCD41 pre-measurement timer callback function
  * @param  context ptr
  */
static void OnScd41TimerEvent(void *context);

/**
  * @brief  SCD41 restart timer callback function (power-cycled single shot, phase 2)
  * @param  context ptr
  */
static void OnScd41RestartTimerEvent(void *context);

/**
  * @brief  SPS30 pre-measurement timer callback function
  * @param  context ptr
  */
static void OnSps30TimerEvent(void *context);

/**
  * @brief  SPS30 fan cleanup timer callback function
  * @param  context ptr
  */
static void OnSps30CleanupTimerEvent(void *context);

/**
  * @brief  Solar sampling timer callback (every SOLAR_SAMPLE_S)
  * @param  context ptr
  */
static void OnSolarTimerEvent(void *context);

/**
  * @brief  One solar sample: INA226 and the PB2 divider into the block statistics
  */
static void SampleSolar(void);

/**
  * @brief  Charger CE timer callback: re-enables charging after the CE pulse
  * @param  context ptr
  */
static void OnChargerCeTimerEvent(void *context);

/**
  * @brief  Reset the BQ25185 safety timer: disable charging via CE,
  *         re-enable after BQ25185_CE_RESET_PULSE_MS (timer driven)
  */
static void ChargerSafetyTimerReset(void);

/**
  * @brief  Charger safety-timer periodic callback: pulses CE to reset the BQ25185 safety timer
  * @param  context ptr
  */
static void OnChargerSafetyTimerEvent(void *context);

/**
  * @brief  Load interval and thresholds from NVM (defaults, or the 2.0 interval, if none stored)
  */
static void Settings_Load(void);

/**
  * @brief  Persist interval and thresholds (assumed already validated)
  * @retval true on success, false on flash write error
  */
static bool Settings_Save(const device_settings_t *next);

/**
  * @brief  Use new settings at once: interval from this moment, thresholds from the next reading
  */
static void Settings_Apply(const device_settings_t *next);

static bool SendSettingsReport(void);

/* USER CODE END PFP */


/**
  * @brief LoRaWAN User credentials
  */
static uint8_t user_dev_eui[8]      = FORMAT32_KEY(LORAWAN_DEVICE_EUI);
static uint8_t user_join_eui[8]     = FORMAT32_KEY(LORAWAN_JOIN_EUI);
static uint8_t user_gen_app_key[16] = FORMAT_KEY(LORAWAN_GEN_APP_KEY);
static uint8_t user_app_key[16]     = FORMAT_KEY(LORAWAN_APP_KEY);
/**
  * @brief  Buffer for rx payload
  */
static uint8_t                  rx_payload[SMTC_MODEM_MAX_LORAWAN_PAYLOAD_LENGTH] = { 0 };

/**
  * @brief  Size of the payload in the rx_payload buffer
  */
static uint8_t                  rx_payload_size = 0;

/**
  * @brief  Metadata of downlink
  */
static smtc_modem_dl_metadata_t rx_metadata     = { 0 };

/**
  * @brief  Remaining downlink payload in modem
  */
static uint8_t                  rx_remaining    = 0;

/**
 * @brief TX counter
 */
static uint8_t                  tx_counter    = 0U;

/**
 * @brief Last SPS30 fan cleaning timestamp
 */
static uint32_t                 last_sps30_clean_timestamp = 0U;

/**
  * @brief LoRaWAN Certification Mode
  */
static bool CertMode = LORAWAN_CERTIFICATION_MODE;

/**
  * @brief Type of Event to generate application Tx
  */
static TxEventType_t EventType = TX_ON_TIMER;

#if defined (LOW_POWER_DISABLE) && (LOW_POWER_DISABLE == 0)
/**
  * @brief Timer to handle the sleep time
  */
static UTIL_TIMER_Object_t SleepTimer;
#endif /* (LOW_POWER_DISABLE) && (LOW_POWER_DISABLE == 0) */

/**
  * Temp buffer to store a FLASH page in RAM when partial replacement is needed
  */
/* NVM snapshots replace the legacy read/erase/rewrite page buffer. */

/**
  * @brief Handler Callbacks
  */
static Callbacks_t Callbacks =
{
  .EventCallback =                EventCallback,
  .RestoreContext =               RestoreContext,
  .StoreContext =                 StoreContext,
  .GetRandomValue =               GetRandomValue,
  .GetBatteryLevel =              GetBatteryLevel,
  .GetTemperatureLevel =          GetTemperatureLevel,
  .SystemReset =                  SystemReset,
};

/* USER CODE BEGIN PV */
/**
  * @brief User application buffer
  */
static uint8_t AppDataBuffer[LORAWAN_APP_DATA_BUFFER_MAX_SIZE];

/**
  * @brief Timer to handle the application Tx Led to toggle

static UTIL_TIMER_Object_t TxLedTimer;
*/
/**
  * @brief Timer to handle the application Rx Led to toggle

static UTIL_TIMER_Object_t RxLedTimer;
*/
/**
  * @brief Timer to handle the application Join Led to toggle

static UTIL_TIMER_Object_t JoinLedTimer;
*/
/**
  * @brief Timer to trigger SCD41 pre-measurement (start stabilisation single shot, phase 1)
  */
static UTIL_TIMER_Object_t Scd41Timer;

/**
  * @brief Timer to discard the SCD41 stabilisation shot and start the useful shot (phase 2)
  */
static UTIL_TIMER_Object_t Scd41RestartTimer;

/**
  * @brief Timer to trigger SPS30 pre-measurement
  */
static UTIL_TIMER_Object_t Sps30Timer;

/**
  * @brief Timer to stop SPS30 fan cleaning
  */
static UTIL_TIMER_Object_t Sps30CleanupTimer;

/**
  * @brief Timer to end the BQ25185 CE pulse (re-enable charging)
  */
static UTIL_TIMER_Object_t ChargerCeTimer;

/**
  * @brief Periodic timer to reset the BQ25185 charger safety timer, independent of the TX loop
  */
static UTIL_TIMER_Object_t ChargerSafetyTimer;

/**
  * @brief Periodic solar sampling timer; posts EVENT_SOLAR only
  */
static UTIL_TIMER_Object_t SolarTimer;

/**
  * @brief Active TX duty cycle in seconds. Defaults to APP_TX_DUTYCYCLE, overridden by a
  *        flash-stored value at boot and by the downlink SET_TX_INTERVAL command at runtime.
  */
static uint32_t tx_dutycycle_s = APP_TX_DUTYCYCLE;

/* Interval and thresholds in effect (firmware 2.1), and their fPort 6 report:
 * after the join, after every 0x14/0x10 (accepted or not), else daily. */
static device_settings_t settings;
static bool settings_from_nvm;
static bool settings_report_due;
static uint32_t settings_reported_at;

enum { EVENT_SCD_START=1U, EVENT_SCD_RESTART=2U, EVENT_SPS_START=4U, EVENT_SPS_STOP=8U, EVENT_SOLAR=16U };
static volatile uint32_t sensor_events;
static power_policy_t power_policy;
static sensor_t battery_sample;
static uint32_t battery_checked_at;
static bool modem_started, credentials_ready, sensors_started, recovery_stopped;
static uint32_t join_started_at, next_join_at, join_backoff_s = 300U;
static bool join_attempt_active;
static uint32_t tx_queued_at;
static bool tx_pending;
static uint16_t tx_failures, sensor_failures;
static uint16_t last_valid_sensors;
static uint8_t failed_uplinks;
static bool shutdown_pending;
static uint32_t next_measurement_at;
static link_check_t link_check;
static bool rejoin_requested;
/* Solar statistics since the last block the modem accepted. */
static solar_acc_t solar_acc;
/* One fPort 99 frame may follow each accepted regular uplink. */
static bool fault_frame_due;
static uint16_t tx_not_sent, tx_rejected;
static uint8_t nvm_errors_reported;
static bool solar_bus_recovered;
static bool install_requested, install_started, install_check_due, install_check_pending;
static uint32_t install_until;
static uint8_t install_uplinks, install_checks;
static bool led_start_phase = true;
/* Power mode the current round's pre-measurements were planned with. */
static power_mode_t planned_mode;

/* USER CODE END PV */

/* Exported functions ---------------------------------------------------------*/
/*
 * -----------------------------------------------------------------------------
 * --- PUBLIC FUNCTIONS DEFINITION ---------------------------------------------
 */

void LoRaWAN_Init(void)
{
  /* USER CODE BEGIN LoRaWAN_Init_LV */
  lr1mac_version_t lorawan_version;
  lr1mac_version_t rp_version;

  /* USER CODE END LoRaWAN_Init_LV */

  /* USER CODE BEGIN LoRaWAN_Init_1 */
  /* Boot report, first in the fPort 99 queue so it leaves in the first
   * frame after the join: restart reason and reset flags, version, and a
   * LSE that needed the second attempt. */
  Fault_Event(FAULT_CODE(FAULT_CAT_SYSTEM, FAULT_SYS_BOOT),
              (uint16_t)(((Runtime_LastFault() & 0xFFU) << 8) | Fault_CompressResetFlags(Runtime_ResetFlags())));
  Fault_Event(FAULT_CODE(FAULT_CAT_SYSTEM, FAULT_SYS_VERSION),
              (uint16_t)((APP_VERSION_MAIN << 8) | APP_VERSION_SUB1));
  if (SystemClock_LseAttempts() > 1U)
    Fault_Event(FAULT_CODE(FAULT_CAT_SYSTEM, FAULT_SYS_LSE_RETRY), SystemClock_LseAttempts());
  /* Every boot while the option byte is missing: no Standby possible. */
  if (!Standby_IwdgReady())
    Fault_Event(FAULT_CODE(FAULT_CAT_SYSTEM, FAULT_SYS_NO_IWDG_STDBY), 0U);

  APP_LOG(TS_OFF, VLEVEL_M, "LoRaWAN End Node LBM\r\n");
  /* Get LoRaWAN APP version*/
  APP_LOG(TS_OFF, VLEVEL_M, "APPLICATION_VERSION: V%X.%X.%X\r\n",
          (uint8_t)(APP_VERSION_MAIN),
          (uint8_t)(APP_VERSION_SUB1),
          (uint8_t)(APP_VERSION_SUB2));

  /* Get MW LoRaWAN info */
  APP_LOG(TS_OFF, VLEVEL_M, "MW_LORAWAN_VERSION:  V%X.%X.%X\r\n",
          (uint8_t)(LORAWAN_VERSION_MAIN),
          (uint8_t)(LORAWAN_VERSION_SUB1),
          (uint8_t)(LORAWAN_VERSION_SUB2));

  /* Get MW SubGhz_Phy info */
  APP_LOG(TS_OFF, VLEVEL_M, "MW_RADIO_VERSION:    V%X.%X.%X\r\n",
          (uint8_t)(SUBGHZ_PHY_VERSION_MAIN),
          (uint8_t)(SUBGHZ_PHY_VERSION_SUB1),
          (uint8_t)(SUBGHZ_PHY_VERSION_SUB2));

  /* Get LoRaWAN Link Layer info */
  memset(&lorawan_version, 0, sizeof(lr1mac_version_t));
  lorawan_version = lorawan_api_get_spec_version(STACK_ID);

  APP_LOG(TS_OFF, VLEVEL_M, "L2_SPEC_VERSION:     V%X.%X.%X\r\n",
          (uint8_t)(lorawan_version.major),
          (uint8_t)(lorawan_version.minor),
          (uint8_t)(lorawan_version.patch));

  /* Get LoRaWAN Regional Parameters info */
  memset(&rp_version, 0, sizeof(lr1mac_version_t));
  rp_version = lorawan_api_get_regional_parameters_version(STACK_ID);
  APP_LOG(TS_OFF, VLEVEL_M, "RP_SPEC_VERSION:     V%X-%X.%X.%X\r\n",
          (uint8_t)(rp_version.revision),
          (uint8_t)(rp_version.major),
          (uint8_t)(rp_version.minor),
          (uint8_t)(rp_version.patch));

  // UTIL_TIMER_Create(&TxLedTimer, LED_PERIOD_TIME, UTIL_TIMER_ONESHOT, OnTxTimerLedEvent, NULL);
  // UTIL_TIMER_Create(&RxLedTimer, LED_PERIOD_TIME, UTIL_TIMER_ONESHOT, OnRxTimerLedEvent, NULL);
  // UTIL_TIMER_Create(&JoinLedTimer, LED_PERIOD_TIME, UTIL_TIMER_PERIODIC, OnJoinTimerLedEvent, NULL);
  UTIL_TIMER_Create(&Scd41Timer, SCD41_PRE_MEASUREMENT_TIME_MS, UTIL_TIMER_ONESHOT, OnScd41TimerEvent, NULL);
  UTIL_TIMER_Create(&Scd41RestartTimer, SCD41_RESTART_TIME_MS, UTIL_TIMER_ONESHOT, OnScd41RestartTimerEvent, NULL);
  UTIL_TIMER_Create(&Sps30Timer, SPS30_PRE_MEASUREMENT_TIME_MS, UTIL_TIMER_ONESHOT, OnSps30TimerEvent, NULL);
  UTIL_TIMER_Create(&Sps30CleanupTimer, SPS30_CLEANING_DURATION_MS, UTIL_TIMER_ONESHOT, OnSps30CleanupTimerEvent, NULL);
  UTIL_TIMER_Create(&ChargerCeTimer, BQ25185_CE_RESET_PULSE_MS, UTIL_TIMER_ONESHOT, OnChargerCeTimerEvent, NULL);
  BQ25185_ChargeEnable();

  /* Independent periodic CE pulse to keep the BQ25185 safety timer from expiring */
  UTIL_TIMER_Create(&ChargerSafetyTimer, BQ25185_SAFETY_RESET_INTERVAL_MS, UTIL_TIMER_PERIODIC, OnChargerSafetyTimerEvent, NULL);
  UTIL_TIMER_Start(&ChargerSafetyTimer);

  /* Solar input: 30 s samples in NORMAL and SAVE (TD_2_0_10). */
  UTIL_TIMER_Create(&SolarTimer, SOLAR_SAMPLE_S * 1000U, UTIL_TIMER_PERIODIC, OnSolarTimerEvent, NULL);
  UTIL_TIMER_Start(&SolarTimer);
  Solar_Reset(&solar_acc);

  /* USER CODE END LoRaWAN_Init_1 */

  /* Both snapshots unreadable on a migrated device is a condition stored in
   * flash: resetting re-reads the same flash and loops forever, killing a
   * station nobody can reach. Carry on with an uninitialised store instead -
   * reads and writes then fail and are counted, the stack falls back to a
   * factory-reset context, and the node keeps measuring and reporting. */
  if (!Nvm_Init()) { Runtime_NoteNvmError(Nvm_LastError()); }

#if defined (LOW_POWER_DISABLE) && (LOW_POWER_DISABLE == 0)
  UTIL_TIMER_Create(&SleepTimer, LED_PERIOD_TIME, UTIL_TIMER_ONESHOT, OnSleepTimerEvent, NULL);
#endif /* (LOW_POWER_DISABLE) && (LOW_POWER_DISABLE == 0) */
  Settings_Load();
  (void)MAX17048_Init();
  (void)EnvSensors_Read(&battery_sample, SENSOR_FLAG_ONLY_BATTERY);
  PowerPolicy_Init(&power_policy, &settings.th, battery_sample.battery_voltage,
                   (battery_sample.valid & SENSOR_VALID_BATTERY) != 0U);
  planned_mode = power_policy.mode;
  battery_checked_at = SysTimeGetMcuTime().Seconds;
  ReportPower();
  ReportNvm();
}

void LoRaWAN_EnableInstallMode(void)
{
  install_requested = true;
}

/* LED1 start phase: short flash per join attempt, double flash on the
 * join, one flash for the first uplink, then dark; dark after 30 min at the
 * latest, joined or not. */
static void StartPhaseFlash(uint8_t count, uint16_t on_ms, bool last)
{
  if (!led_start_phase) return;
  if (SysTimeGetMcuTime().Seconds >= LED_START_PHASE_S)
  {
    led_start_phase = false;
    return;
  }
  Led_Flash(LED_1, count, on_ms, 200U);
  if (last) led_start_phase = false;
}

static bool Installing(void)
{
  return install_started && (int32_t)(SysTimeGetMcuTime().Seconds - install_until) < 0;
}

void LoRaWAN_Process(void)
{
  Fault_Tick(SysTimeGetMcuTime().Seconds);
  ServicePower();
  uint32_t sleep_time_ms = RUNTIME_MAX_SLEEP_MS;
  if (power_policy.mode != POWER_RECOVERY)
  {
    if (!modem_started)
    {
      smtc_modem_init(&Callbacks);
      smtc_modem_set_certification_mode(STACK_ID, CertMode);
      smtc_modem_set_crystal_error_ppm(BSP_CRYSTAL_ERROR);
      modem_started = true;
    }
    if (!sensors_started)
    {
      EnvSensors_Init();
      sensors_started = true;
      recovery_stopped = false;
    }
    sleep_time_ms = smtc_modem_run_engine();
    ServiceJoin();
    ProcessSensorEvents();
    /* Sensor work / joins can enqueue modem tasks: recompute before sleep. */
    sleep_time_ms = smtc_modem_run_engine();
    if (tx_pending && (uint32_t)(SysTimeGetMcuTime().Seconds - tx_queued_at) > 900U)
      Runtime_Fault(RUNTIME_FAULT_MODEM);
  }
  else
  {
    /* Expected dormancy is progress too; no radio or heavy sensor startup.
     * No solar sampling either; the INA226 stays powered down. */
    uint32_t primask = __get_PRIMASK();
    __disable_irq();
    sensor_events &= ~(uint32_t)EVENT_SOLAR;
    __set_PRIMASK(primask);
    Runtime_ExpectProgress(POWER_CHECK_S + 120U);
  }
  if (sleep_time_ms > RUNTIME_MAX_SLEEP_MS) sleep_time_ms = RUNTIME_MAX_SLEEP_MS;
#if defined (LOW_POWER_DISABLE) && (LOW_POWER_DISABLE == 0)
  /* Recheck pending work under the same interrupt mask used by STOP2. */
  uint32_t primask = __get_PRIMASK();
  __disable_irq();
  if (sleep_time_ms > 0U && sensor_events == 0U &&
      (power_policy.mode == POWER_RECOVERY || !modem_started || !smtc_modem_is_irq_flag_pending()))
  {
    UTIL_TIMER_SetPeriod(&SleepTimer, sleep_time_ms);
    UTIL_TIMER_Start(&SleepTimer);
    UTIL_LPM_EnterLowPower();
  }
  __set_PRIMASK(primask);
#endif
}

static void ReadBattery(void)
{
  (void)EnvSensors_Read(&battery_sample, SENSOR_FLAG_ONLY_BATTERY);
  battery_checked_at = SysTimeGetMcuTime().Seconds;
  PowerPolicy_Update(&power_policy, battery_sample.battery_voltage,
                     (battery_sample.valid & SENSOR_VALID_BATTERY) != 0U,
                     battery_checked_at);
  ReportPower();
}

/* Supply states on fPort 99: SAVE 0x0320, RECOVERY 0x0321 and three invalid
 * readings 0x0323, each on entry and on exit, with the battery voltage. */
static void ReportPower(void)
{
  uint16_t mv = (battery_sample.valid & SENSOR_VALID_BATTERY) ? battery_sample.battery_voltage : 0xFFFFU;
  Fault_SetState(FAULT_CODE(FAULT_CAT_SUPPLY, FAULT_SUPPLY_SAVE), power_policy.mode == POWER_SAVE, mv);
  Fault_SetState(FAULT_CODE(FAULT_CAT_SUPPLY, FAULT_SUPPLY_RECOVERY), power_policy.mode == POWER_RECOVERY, mv);
  Fault_SetState(FAULT_CODE(FAULT_CAT_SUPPLY, FAULT_SUPPLY_INVALID), power_policy.failures >= 3U, mv);
}

static void ReportNvm(void)
{
  uint8_t errors = Runtime_NvmErrorCount();
  if (errors == nvm_errors_reported) return;
  nvm_errors_reported = errors;
  Fault_Event(FAULT_CODE(FAULT_CAT_SYSTEM, FAULT_SYS_NVM), Runtime_LastNvmError());
}

/* True when a frame went to the modem. */
static bool SendFaultFrame(void)
{
  uint8_t frame[FAULT_FRAME_MAX_LEN];
  uint8_t n = Fault_BuildFrame(frame);
  if (n == 0U) return false;
  /* Unconfirmed; rejected (duty cycle) means the entries wait a round. */
  if (smtc_modem_request_uplink(STACK_ID, TX_PORT_FAULTS, false, frame, n) != SMTC_MODEM_RC_OK)
    return false;
  Fault_FrameAccepted();
  return true;
}

/* The settings report on fPort 6. Its own unconfirmed uplink right after a
 * regular one, never in RECOVERY; a rejected request stays due. True when the
 * modem took it. */
static bool SendSettingsReport(void)
{
  if (power_policy.mode == POWER_RECOVERY) return false;
  settings_report_info_t info = {
    .fw_major = APP_VERSION_MAIN,
    .fw_minor = APP_VERSION_SUB1,
    .hardware = BOARD_HW_REV,
    .mode = power_policy.mode,
    .flags = (uint16_t)((Standby_IwdgReady() ? SETTINGS_FLAG_IWDG_STDBY : 0U) |
                        (settings_from_nvm ? SETTINGS_FLAG_FROM_NVM : 0U) |
                        (PULSE_COUNTERS_ENABLED ? SETTINGS_FLAG_PULSE : 0U)),
  };
  uint8_t report[SETTINGS_REPORT_LEN];
  DeviceSettings_BuildReport(&settings, &info, report);
  if (smtc_modem_request_uplink(STACK_ID, SETTINGS_REPORT_PORT, false, report, sizeof report) != SMTC_MODEM_RC_OK)
    return false;
  settings_report_due = false;
  settings_reported_at = SysTimeGetMcuTime().Seconds;
  return true;
}

static void StopSensorTimers(void)
{
  UTIL_TIMER_Stop(&Scd41Timer);
  UTIL_TIMER_Stop(&Scd41RestartTimer);
  UTIL_TIMER_Stop(&Sps30Timer);
  UTIL_TIMER_Stop(&Sps30CleanupTimer);
  uint32_t primask = __get_PRIMASK();
  __disable_irq();
  sensor_events = 0U;
  __set_PRIMASK(primask);
}

static void ServicePower(void)
{
  bool checked = (uint32_t)(SysTimeGetMcuTime().Seconds - battery_checked_at) >= POWER_CHECK_S;
  if (checked) ReadBattery();
  if (power_policy.mode == POWER_RECOVERY)
  {
    if (!recovery_stopped)
    {
      StopSensorTimers();
      if (modem_started)
      {
        (void)smtc_modem_leave_network(STACK_ID);
        (void)smtc_modem_alarm_clear_timer();
      }
      tx_pending = false;
      join_attempt_active = false;
      next_join_at = SysTimeGetMcuTime().Seconds;
      tx_counter = 0U;
      shutdown_pending = true;
    }
    if (!recovery_stopped || (checked && shutdown_pending))
    {
      /* Also after a MCU-only reset: sensors may still be measuring. */
      shutdown_pending = EnvSensors_Sleep() != 0;
      if (shutdown_pending) (void)I2C2_RecoverBus();
    }
    sensors_started = false;
    recovery_stopped = true;
    /* Deep discharge: Standby with an hourly RTC wake-up, once the sensors
     * are asleep and only when the IWDG stops in Standby (0x0544 otherwise). */
    if (power_policy.standby && !shutdown_pending && Standby_IwdgReady())
      Standby_Enter(power_policy.th.resume);
  }
  else recovery_stopped = false;
}

static void ServiceJoin(void)
{
  if (!credentials_ready || power_policy.mode == POWER_RECOVERY) return;
  uint32_t now = SysTimeGetMcuTime().Seconds;
  if (rejoin_requested)
  {
    /* Three days without LinkCheckAns: the server context or the gateway is
     * gone. Leave and rejoin; the JOINED event restarts the uplink cycle. */
    rejoin_requested = false;
    StopSensorTimers();
    (void)smtc_modem_alarm_clear_timer();
    (void)smtc_modem_leave_network(STACK_ID);
    tx_pending = false;
    join_attempt_active = false;
    join_backoff_s = 300U;
    next_join_at = now;
  }
  smtc_modem_status_mask_t status = 0;
  if (smtc_modem_get_status(STACK_ID, &status) != SMTC_MODEM_RC_OK) return;
  if (status & SMTC_MODEM_STATUS_JOINED)
  {
    join_attempt_active = false;
    join_backoff_s = 300U;
    return;
  }
  if (join_attempt_active)
  {
    if ((uint32_t)(now - join_started_at) < 300U) return;
    (void)smtc_modem_leave_network(STACK_ID);
    join_attempt_active = false;
    next_join_at = now + join_backoff_s;
    Runtime_ExpectProgress(join_backoff_s + 600U);
    if (join_backoff_s < 3600U) join_backoff_s *= 2U;
    if (join_backoff_s > 3600U) join_backoff_s = 3600U;
    return;
  }
  if ((int32_t)(now - next_join_at) < 0) return;
  if (smtc_modem_join_network(STACK_ID) == SMTC_MODEM_RC_OK)
  {
    StartPhaseFlash(1U, 50U, false);
    join_attempt_active = true;
    join_started_at = now;
    Runtime_ExpectProgress(600U);
  }
  else next_join_at = now + 60U;
}

static void ProcessSensorEvents(void)
{
  uint32_t primask = __get_PRIMASK();
  __disable_irq();
  uint32_t pending = sensor_events;
  sensor_events = 0U;
  __set_PRIMASK(primask);
  if (pending & EVENT_SOLAR)
  {
    pending &= ~(uint32_t)EVENT_SOLAR;
    if (power_policy.mode != POWER_RECOVERY) SampleSolar();
  }
  if (!pending) return;
  ReadBattery();
  ServicePower();
  if (power_policy.mode == POWER_RECOVERY) return;
  int32_t result = 0;
  if (pending & EVENT_SPS_STOP)
  {
    result |= SPS30_StopMeasurement();
    result |= SPS30_Sleep();
  }
  /* Do not start a stale premeasurement after its intended uplink. */
  if ((int32_t)(SysTimeGetMcuTime().Seconds - next_measurement_at) >= 0)
    pending &= EVENT_SPS_STOP;
  if (!(battery_sample.valid & SENSOR_VALID_BATTERY)) return;
  if (SCD41_ENABLED && (pending & EVENT_SCD_START))
    result |= EnvSensors_StartPreMeasurement(SENSOR_FLAG_CO2);
  if (SCD41_ENABLED && (pending & EVENT_SCD_RESTART))
    result |= EnvSensors_RestartPreMeasurement(SENSOR_FLAG_CO2);
  /* The PM measurement (1.6 C each) runs in NORMAL only. */
  if ((pending & EVENT_SPS_START) && power_policy.mode == POWER_NORMAL)
    result |= EnvSensors_StartPreMeasurement(SENSOR_FLAG_SPS30);
  if (result != 0)
  {
    if (sensor_failures != UINT16_MAX) sensor_failures++;
    (void)I2C2_RecoverBus();
  }
}

static void SystemReset(void)
{
  __disable_irq();
  HAL_NVIC_SystemReset();   /* Restart system */
}

static uint32_t GetRandomValue(void)
{
  uint32_t rand_nb = 0;
  // Init and enable RNG
  hrng.Instance = RNG;
  hrng.Init.ClockErrorDetection = RNG_CED_ENABLE;

  if (HAL_RNG_Init(&hrng) != HAL_OK)
  {
    Error_Handler();
  }

  // Wait for data ready interrupt: 42+4 RNG clock cycles
  if (HAL_RNG_GenerateRandomNumber(&hrng, &rand_nb) != HAL_OK)
  {
    Error_Handler();
  }

  // Disable RNG
  HAL_RNG_DeInit(&hrng);

  return rand_nb;
}

static bool ContextRange(modem_context_type_t type, uint32_t offset, uint32_t size, uint32_t *address)
{
  uint32_t base, capacity;
  switch (type)
  {
    case CONTEXT_LORAWAN_STACK: base=0; capacity=LORAWAN_CONTEXT_SIZE; break;
    case CONTEXT_MODEM: base=LORAWAN_CONTEXT_SIZE; capacity=MODEM_CONTEXT_SIZE; break;
    case CONTEXT_SECURE_ELEMENT: base=LORAWAN_CONTEXT_SIZE+MODEM_CONTEXT_SIZE; capacity=SECURE_ELEMENT_CONTEXT_SIZE; break;
    default: return false;
  }
  if (offset > capacity || size > capacity-offset) return false;
  *address=base+offset;
  return true;
}

/* A failed restore leaves the caller's buffer untouched; every caller zeroes
 * it first and CRC-checks the result, so it falls back to a factory reset. */
static void RestoreContext(const modem_context_type_t type, uint32_t offset, uint8_t *buffer, const uint32_t size)
{
  uint32_t address;
  if (!ContextRange(type,offset,size,&address)) { Runtime_NoteNvmError(NVM_ERR_CONTEXT); return; }
  if (!Nvm_Read(address,buffer,size)) { Runtime_NoteNvmError(Nvm_LastError()); }
}

static void StoreContext(const modem_context_type_t type, uint32_t offset, const uint8_t *buffer, const uint32_t size)
{
  uint32_t address;
  /* A persistence failure must not reset. The DevNonce lives in RAM and keeps
   * incrementing; a reset restarts the join from the same persisted state and
   * so causes the nonce reuse it was meant to prevent, right in the JoinAccept
   * window. Count it and report it in the 0x12 diagnostic instead. */
  if (!ContextRange(type,offset,size,&address)) { Runtime_NoteNvmError(NVM_ERR_CONTEXT); return; }
  if (!Nvm_Write(address,buffer,size)) { Runtime_NoteNvmError(Nvm_LastError()); }
}

static void EventCallback(void)
{
  smtc_modem_event_t current_event;
  uint8_t            event_pending_count;
  uint8_t            stack_id = STACK_ID;
  smtc_modem_status_mask_t status_mask = 0;

  /* Continue to read modem event until all event has been processed */
  do
  {
    /* Read modem event */
    smtc_modem_return_code_t event_status = smtc_modem_get_event(&current_event, &event_pending_count);
    if (event_status == SMTC_MODEM_RC_NO_EVENT) return;
    if (event_status != SMTC_MODEM_RC_OK) Runtime_Fault(RUNTIME_FAULT_MODEM);

    switch (current_event.event_type)
    {
      case SMTC_MODEM_EVENT_RESET:
      {
        APP_LOG(TS_OFF, VLEVEL_M, "Event received: RESET\r\n");

        uint8_t eui_bits = 0U;
        for (uint8_t i=0; i<sizeof user_dev_eui; ++i) eui_bits |= user_dev_eui[i];
        if (eui_bits == 0U) GetUniqueId(user_dev_eui);
        APP_LOG(TS_OFF, VLEVEL_M, "DevEUI: %02X%02X%02X%02X%02X%02X%02X%02X\r\n",
                user_dev_eui[0],user_dev_eui[1],user_dev_eui[2],user_dev_eui[3],
                user_dev_eui[4],user_dev_eui[5],user_dev_eui[6],user_dev_eui[7]);

        /* Set user credentials */
        ASSERT_SMTC_MODEM_RC(smtc_modem_set_deveui(stack_id, user_dev_eui));
        ASSERT_SMTC_MODEM_RC(smtc_modem_set_joineui(stack_id, user_join_eui));
        ASSERT_SMTC_MODEM_RC(smtc_modem_set_appkey(stack_id, user_gen_app_key));
        ASSERT_SMTC_MODEM_RC(smtc_modem_set_nwkkey(stack_id, user_app_key));

        /* Set user region */
        ASSERT_SMTC_MODEM_RC(smtc_modem_set_region(stack_id, ACTIVE_REGION));

        /* Print Security material */
        /* Never print secret keys, including in debug builds. */
        CertMode = (smtc_modem_is_certification_port_disabled(STACK_ID)) ? 0 : CertMode;
        if (CertMode == false)
        {
          /* Schedule a Join LoRaWAN network */
          ASSERT_SMTC_MODEM_RC(smtc_modem_set_join_duty_cycle_backoff_bypass(stack_id, false));
          credentials_ready = true;
          next_join_at = SysTimeGetMcuTime().Seconds;
        }
        break;
      }
      case SMTC_MODEM_EVENT_ALARM:
        APP_LOG(TS_OFF, VLEVEL_M,  "Event received: ALARM\r\n");
        if (CertMode == true)
        {
          ASSERT_SMTC_MODEM_RC(smtc_modem_alarm_clear_timer());
        }
        else
        {
          /* Send periodical uplink */
          SendTxData(LORAWAN_USER_APP_PORT);
        }
        break;

      case SMTC_MODEM_EVENT_JOINED:
        APP_LOG(TS_OFF, VLEVEL_M,  "Event received: JOINED\r\n");
        APP_LOG(TS_OFF, VLEVEL_H,  "Modem is now joined \r\n");
        /* USER CODE BEGIN EventCallback_1 */
        // if (JoinLedTimer.IsRunning)
        // {
        //   UTIL_TIMER_Stop(&JoinLedTimer);
        //   HAL_GPIO_WritePin(LED3_GPIO_Port, LED3_Pin, GPIO_PIN_RESET); /* LED_RED */
        // }
        /* USER CODE END EventCallback_1 */
        StartPhaseFlash(2U, 100U, false);
        /* The backend learns the values after every join, behind the boot frame. */
        settings_report_due = true;
        /* Static node: let the network server drive the data rate. */
        ASSERT_SMTC_MODEM_RC(smtc_modem_adr_set_profile(STACK_ID, SMTC_MODEM_ADR_PROFILE_NETWORK_CONTROLLED, NULL));
        {
          uint8_t days = LinkCheck_Joined(&link_check, SysTimeGetMcuTime().Seconds);
          if (days != 0U) Fault_Event(FAULT_CODE(FAULT_CAT_RADIO, FAULT_RADIO_REJOIN), days);
          if (install_requested && !install_started)
          {
            install_started = true;
            install_until = SysTimeGetMcuTime().Seconds + INSTALL_DURATION_S;
          }
        }
        if (CertMode == false)
        {
          /* Send first periodical uplink */
          SendTxData(LORAWAN_USER_APP_PORT);
        }
        break;

      case SMTC_MODEM_EVENT_TXDONE:
        tx_pending = false;
        if (current_event.event_data.txdone.status == SMTC_MODEM_EVENT_TXDONE_NOT_SENT)
        {
          if (tx_not_sent != UINT16_MAX) tx_not_sent++;
          Fault_Count(FAULT_CODE(FAULT_CAT_RADIO, FAULT_RADIO_TX_FAILED));
        }
        /* At most one extra uplink per TXDONE: the fault frame first, the
         * settings report with the TXDONE that follows it. */
        {
          bool sent_extra = false;
          if (fault_frame_due)
          {
            fault_frame_due = false;
            /* Urgent entries now, the rest at most hourly (fault_report.h). */
            if (Fault_FrameDue()) sent_extra = SendFaultFrame();
          }
          if ((uint32_t)(SysTimeGetMcuTime().Seconds - settings_reported_at) >= SETTINGS_REPORT_PERIOD_S)
            settings_report_due = true;
          if (!sent_extra && settings_report_due &&
              current_event.event_data.txdone.status != SMTC_MODEM_EVENT_TXDONE_NOT_SENT)
            (void)SendSettingsReport();
        }
        if (install_check_due)
        {
          install_check_due = false;
          if (smtc_modem_trig_lorawan_mac_request(STACK_ID, SMTC_MODEM_LORAWAN_MAC_REQ_LINK_CHECK) == SMTC_MODEM_RC_OK)
          {
            install_checks++;
            install_check_pending = true;
          }
        }
        if (LinkCheck_Due(&link_check, SysTimeGetMcuTime().Seconds) &&
            smtc_modem_trig_lorawan_mac_request(STACK_ID, SMTC_MODEM_LORAWAN_MAC_REQ_LINK_CHECK) == SMTC_MODEM_RC_OK)
        {
          /* LBM sends the request as its own MAC-only uplink. */
          LinkCheck_Requested(&link_check, SysTimeGetMcuTime().Seconds);
        }
        APP_LOG(TS_OFF, VLEVEL_M,  "Event received: TXDONE\r\n");
        APP_LOG(TS_OFF, VLEVEL_H,  "Transmission done \r\n");
        smtc_modem_get_status(STACK_ID, &status_mask);
        /* First uplink after the join went out: last flash of the start phase. */
        if ((status_mask & SMTC_MODEM_STATUS_JOINED) &&
            current_event.event_data.txdone.status != SMTC_MODEM_EVENT_TXDONE_NOT_SENT)
          StartPhaseFlash(1U, 50U, true);
        /* USER CODE BEGIN EventCallback_2 */
        /* Check if the device has already joined a network */
        // if ((JoinLedTimer.IsRunning) && (status_mask & SMTC_MODEM_STATUS_JOINED) == SMTC_MODEM_STATUS_JOINED)
        // {
        //   UTIL_TIMER_Stop(&JoinLedTimer);
        //   HAL_GPIO_WritePin(LED3_GPIO_Port, LED3_Pin, GPIO_PIN_RESET); /* LED_RED */
        // }
        /* USER CODE END EventCallback_2 */
        break;

      case SMTC_MODEM_EVENT_DOWNDATA:
        APP_LOG(TS_OFF, VLEVEL_M,  "Event received: DOWNDATA\r\n");
        /* USER CODE BEGIN EventCallback_3 */
        //HAL_GPIO_WritePin(LED1_GPIO_Port, LED1_Pin, GPIO_PIN_SET); /* LED_BLUE */
        // UTIL_TIMER_Start(&RxLedTimer);
        /* USER CODE END EventCallback_3 */
        /* Get downlink data */
        if (smtc_modem_get_downlink_data(rx_payload, &rx_payload_size, &rx_metadata, &rx_remaining) != SMTC_MODEM_RC_OK)
          break;
        APP_LOG(TS_OFF, VLEVEL_M, "Data received on port %u\r\n", rx_metadata.fport);
        if (rx_payload_size == 0U)
        {
          APP_LOG(TS_ON, VLEVEL_M, "Ignoring empty downlink payload on port %u\r\n", rx_metadata.fport);
          break;
        }

        if (rx_remaining > 0U)
        {
          APP_LOG(TS_ON, VLEVEL_M, "Downlink payload truncated, remaining=%u\r\n", (unsigned)rx_remaining);
        }

        processRxData(rx_payload, rx_payload_size, &rx_metadata);
        /* APP_LOG(TS_OFF, VLEVEL_M, "Received payload", rx_payload, rx_payload_size ); */
        break;

      case SMTC_MODEM_EVENT_JOINFAIL:
        APP_LOG(TS_OFF, VLEVEL_M,  "Event received: JOINFAIL\r\n");
        /* LBM retries on its own: each failed attempt marks the next one. */
        StartPhaseFlash(1U, 50U, false);
        smtc_modem_get_status(STACK_ID, &status_mask);
        /* USER CODE BEGIN EventCallback_4 */
        /* Check if the device has already joined a network */
        // if ((!JoinLedTimer.IsRunning) && (status_mask & SMTC_MODEM_STATUS_JOINED) != SMTC_MODEM_STATUS_JOINED)
        // {
        //   UTIL_TIMER_Start(&JoinLedTimer);
        // }
        /* USER CODE END EventCallback_4 */
        break;

      case SMTC_MODEM_EVENT_ALCSYNC_TIME:
        APP_LOG(TS_OFF, VLEVEL_M,  "Event received: ALCSync service TIME\r\n");
        break;

      case SMTC_MODEM_EVENT_LINK_CHECK:
      {
        APP_LOG(TS_OFF, VLEVEL_M,  "Event received: LINK_CHECK\r\n");
        bool answered = current_event.event_data.link_check.status == SMTC_MODEM_EVENT_MAC_REQUEST_ANSWERED;
        if (install_check_pending)
        {
          /* Installation: one flash per gateway (max 5), one long flash for
           * no answer. Unanswered installation checks are no silent day. */
          uint8_t margin = 0U, gateways = 0U;
          install_check_pending = false;
          if (answered && smtc_modem_get_lorawan_link_check_data(STACK_ID, &margin, &gateways) == SMTC_MODEM_RC_OK &&
              gateways > 0U)
            Led_Flash(LED_1, gateways > 5U ? 5U : gateways, 150U, 350U);
          else
            Led_Flash(LED_1, 1U, 1000U, 0U);
          if (!answered) break;
        }
        if (LinkCheck_Result(&link_check, answered))
        {
          rejoin_requested = true;
        }
        break;
      }

      case SMTC_MODEM_EVENT_CLASS_B_PING_SLOT_INFO:
        APP_LOG(TS_OFF, VLEVEL_M,  "Event received: CLASS_B_PING_SLOT_INFO\r\n");
        break;

      case SMTC_MODEM_EVENT_CLASS_B_STATUS:
        APP_LOG(TS_OFF, VLEVEL_M,  "Event received: CLASS_B_STATUS\r\n");
        break;

      case SMTC_MODEM_EVENT_LORAWAN_MAC_TIME:
        APP_LOG(TS_OFF, VLEVEL_L,  "Event received: LORAWAN MAC TIME\r\n");
        break;

      case SMTC_MODEM_EVENT_LORAWAN_FUOTA_DONE:
      {
        bool status = current_event.event_data.fuota_status.successful;
        if (status == true)
        {
          APP_LOG(TS_OFF, VLEVEL_M,  "Event received: FUOTA SUCCESSFUL\r\n");
        }
        else
        {
          APP_LOG(TS_OFF, VLEVEL_L,  "Event received: FUOTA FAIL\r\n");
        }
        break;
      }

      case SMTC_MODEM_EVENT_NO_MORE_MULTICAST_SESSION_CLASS_C:
        APP_LOG(TS_OFF, VLEVEL_M,  "Event received: MULTICAST CLASS_C STOP\r\n");
        break;

      case SMTC_MODEM_EVENT_NO_MORE_MULTICAST_SESSION_CLASS_B:
        APP_LOG(TS_OFF, VLEVEL_M,  "Event received: MULTICAST CLASS_B STOP\r\n");
        break;

      case SMTC_MODEM_EVENT_NEW_MULTICAST_SESSION_CLASS_C:
        APP_LOG(TS_OFF, VLEVEL_M,  "Event received: New MULTICAST CLASS_C \r\n");
        break;

      case SMTC_MODEM_EVENT_NEW_MULTICAST_SESSION_CLASS_B:
        APP_LOG(TS_OFF, VLEVEL_M,  "Event received: New MULTICAST CLASS_B\r\n");
        break;

      case SMTC_MODEM_EVENT_FIRMWARE_MANAGEMENT:
        APP_LOG(TS_OFF, VLEVEL_M,  "Event received: FIRMWARE_MANAGEMENT\r\n");
        if (current_event.event_data.fmp.status == SMTC_MODEM_EVENT_FMP_REBOOT_IMMEDIATELY)
        {
          HAL_NVIC_SystemReset();
        }
        break;

      case SMTC_MODEM_EVENT_STREAM_DONE:
        APP_LOG(TS_OFF, VLEVEL_M,  "Event received: STREAM_DONE\r\n");
        break;

      case SMTC_MODEM_EVENT_UPLOAD_DONE:
        APP_LOG(TS_OFF, VLEVEL_M,  "Event received: UPLOAD_DONE\r\n");
        break;

      case SMTC_MODEM_EVENT_DM_SET_CONF:
        APP_LOG(TS_OFF, VLEVEL_M,  "Event received: DM_SET_CONF\r\n");
        break;

      case SMTC_MODEM_EVENT_MUTE:
        APP_LOG(TS_OFF, VLEVEL_M,  "Event received: MUTE\r\n");
        break;
      case SMTC_MODEM_EVENT_REGIONAL_DUTY_CYCLE:
      {
        uint8_t duty_cycle_status = current_event.event_data.regional_duty_cycle.status;
        (void)duty_cycle_status;
        APP_LOG(TS_OFF, VLEVEL_M,  "Event received: DUTY_CYCLE b"
                                   "usy %d\r\n", duty_cycle_status);
      }
      break;
      default:
        APP_LOG(TS_OFF, VLEVEL_M,  "Unknown event %u\r\n", current_event.event_type);
        break;
    }
  } while (event_pending_count > 0);
}

static void append_u16_be(uint8_t *buffer, uint8_t *index, uint16_t value)
{
  buffer[*index] = (uint8_t)((value >> 8) & 0xFFU);
  (*index)++;
  buffer[*index] = (uint8_t)(value & 0xFFU);
  (*index)++;
}

static void BuildBlock(payload_block_t *block)
{
  solar_block_t solar;
  MAX17048_Gauge_t gauge;

  Solar_Block(&solar_acc, &solar);
  block->solar_mv = solar.v_mv;
  block->solar_01ma = solar.i_01ma;
  block->solar_mw = solar.p_mw;
  block->solar_01mwh = solar.e_01mwh;
  block->sun_s = solar.sun_s;
  block->solar_adc_mv = solar.adc_mv;
  /* Also re-acknowledges a pending MAX17048 alert; sentinels on failure. */
  (void)MAX17048_ReadGauge(&gauge);
  block->soc_x100 = gauge.soc_x100;
  block->crate_x100 = gauge.crate_x100;
  bool temperature_ok = SYS_ReadBoardTemperature(&block->board_t_x100);
  if (!temperature_ok) block->board_t_x100 = INT16_MIN;
  Fault_ComponentResult(FAULT_COMP_TEMP_SENSOR, temperature_ok, 0U);
  PulseCounter_Read(&block->count1, &block->count2);
}

static void CommitBlock(const payload_block_t *block)
{
  Solar_Reset(&solar_acc);
  PulseCounter_Commit(block->count1, block->count2);
}

static void SendTxData(uint8_t port)
{
  /* USER CODE BEGIN SendTxData_1 */
  sensor_t sensor_data;
  uint8_t bufferSize = 0;
  uint8_t uplink_port = PAYLOAD_PORT_BASE;

  (void)port;

  ReadBattery();
  ServicePower();
  if (power_policy.mode == POWER_RECOVERY) return;
  if (!(battery_sample.valid & SENSOR_VALID_BATTERY))
  {
    (void)smtc_modem_alarm_start_timer(POWER_CHECK_S);
    Runtime_ExpectProgress(POWER_CHECK_S + 120U);
    return;
  }
  ReportNvm();
  /* Installation rounds send port 2 only and leave the round counter alone,
   * so the normal cycle starts fresh afterwards. */
  bool installing = Installing();
  if (!installing)
  {
    /* Increment tx_counter */
    tx_counter++;
    if (tx_counter > POWER_ROUNDS)
    {
      tx_counter = 1U;
    }
  }

  /* Sensors for this round from the adaptive plan (TD_2_0_17). Only what
   * both the planning mode and the current mode ask for: a sensor that was
   * not pre-measured would return stale values, and one that was started but
   * is no longer wanted is put back to sleep. */
  uint8_t planned = installing ? 0U : PowerPolicy_Measurements(planned_mode, tx_counter);
  uint8_t wanted = (uint8_t)(planned & PowerPolicy_Measurements(power_policy.mode, tx_counter));
  uint8_t sensor_flags = 0U;
  if (SCD41_ENABLED && (wanted & POWER_MEASURE_CO2)) { sensor_flags |= SENSOR_FLAG_CO2; }
  if (wanted & POWER_MEASURE_PM) { sensor_flags |= SENSOR_FLAG_SPS30; }
  if ((planned & POWER_MEASURE_PM) && !(wanted & POWER_MEASURE_PM))
  {
    (void)SPS30_StopMeasurement();
    (void)SPS30_Sleep();
  }

  /* Read sensors */
  EnvSensors_Read(&sensor_data, sensor_flags);
  last_valid_sensors = sensor_data.valid;
  uint16_t expected = SENSOR_VALID_BATTERY | SENSOR_VALID_RHT | SENSOR_VALID_PRESSURE | SENSOR_VALID_UV;
  if (sensor_flags & SENSOR_FLAG_CO2) expected |= SENSOR_VALID_CO2;
  if (sensor_flags & SENSOR_FLAG_SPS30) expected |= SENSOR_VALID_PM;
  if ((sensor_data.valid & expected) != expected) if (sensor_failures != UINT16_MAX) sensor_failures++;

  /* Log raw stored values (scaling noted in unit label). Receiver / human
   * reader converts: T/100 = degC, RH/100 = %, P/10 = hPa. */
  APP_LOG(TS_ON, VLEVEL_M, "Sensors: T=%d [0.01degC], RH=%u [0.01%%], P=%u [0.1hPa], VBAT=%u mV\r\n",
          (int)sensor_data.temperature,
          (unsigned)sensor_data.humidity,
          (unsigned)sensor_data.pressure,
          (unsigned)sensor_data.battery_voltage);

  APP_LOG(TS_ON, VLEVEL_M, "LTR390: UVI=%u.%02u\r\n",
          (unsigned)(sensor_data.uvi_x100 / 100U),
          (unsigned)(sensor_data.uvi_x100 % 100U));

  if (sensor_flags & SENSOR_FLAG_CO2)
  {
    APP_LOG(TS_ON, VLEVEL_M, "SCD41: CO2=%u ppm\r\n", (unsigned int)sensor_data.co2_ppm);
  }

  if (sensor_flags & SENSOR_FLAG_SPS30)
  {
    APP_LOG(TS_ON, VLEVEL_M, "SPS30 MC: PM1.0=%u PM2.5=%u PM4.0=%u PM10.0=%u [0.1 ug/m3]\r\n",
            (unsigned)sensor_data.pm1_0,
            (unsigned)sensor_data.pm2_5,
            (unsigned)sensor_data.pm4_0,
            (unsigned)sensor_data.pm10_0);
    APP_LOG(TS_ON, VLEVEL_M, "SPS30 NC: PM0.5=%u PM1.0=%u PM2.5=%u PM4.0=%u PM10=%u [0.1 #/cm3]\r\n",
            (unsigned)sensor_data.nc_0_5,
            (unsigned)sensor_data.nc_1_0,
            (unsigned)sensor_data.nc_2_5,
            (unsigned)sensor_data.nc_4_0,
            (unsigned)sensor_data.nc_10_0);
    APP_LOG(TS_ON, VLEVEL_M, "SPS30 TypSize=%u [nm]\r\n", (unsigned)sensor_data.typ_size);
  }

  uplink_port = Payload_Port(sensor_flags);

  if (sensor_flags & SENSOR_FLAG_SPS30)
  {
    uint32_t current_time_s = SysTimeGetMcuTime().Seconds;
    bool cleaning_triggered = false;

    if (((current_time_s - last_sps30_clean_timestamp) > (SPS30_FAN_CLEAN_INTERVAL_HOURS * 3600U)) &&
        (sensor_data.battery_voltage > 4120))
    {
      APP_LOG(TS_OFF, VLEVEL_M, "Manual SPS30 fan cleaning (VBat=%u mV)\r\n", (unsigned)sensor_data.battery_voltage);
      if (SPS30_StartFanCleaning() == SPS30_STATUS_OK)
      {
        last_sps30_clean_timestamp = current_time_s;
        UTIL_TIMER_Start(&Sps30CleanupTimer);
        cleaning_triggered = true;
      } else
      {
        APP_LOG(TS_OFF, VLEVEL_M, "Failed to start SPS30 fan cleaning\r\n");
      }
    }

    if (!cleaning_triggered)
    {
      if (SPS30_StopMeasurement() != SPS30_STATUS_OK || SPS30_Sleep() != SPS30_STATUS_OK)
      {
        if (sensor_failures != UINT16_MAX) sensor_failures++;
        (void)I2C2_RecoverBus();
        (void)SPS30_Init();
      }
    }
  }

  /* Ports 2 and 3 carry the block (solar, gauge, board temperature,
   * counters); port 4 rounds leave it to the next block. */
  payload_block_t block;
  bool has_block = (uplink_port != PAYLOAD_PORT_FULL);
  if (has_block) BuildBlock(&block);
  bufferSize = Payload_Encode(uplink_port, &sensor_data, &block, AppDataBuffer);

  APP_LOG(TS_ON, VLEVEL_M, "Uplink payload: fPort=%u, %u bytes\r\n", (unsigned)uplink_port, (unsigned)bufferSize);

  // if (JoinLedTimer.IsRunning)
  // {
  //   UTIL_TIMER_Stop(&JoinLedTimer);
  //   HAL_GPIO_WritePin(LED3_GPIO_Port, LED3_Pin, GPIO_PIN_RESET);
  // }

  smtc_modem_return_code_t tx_status = smtc_modem_request_uplink(STACK_ID, uplink_port, false, AppDataBuffer, bufferSize);
  if (tx_status == SMTC_MODEM_RC_OK)
  {
    if (!tx_pending) tx_queued_at = SysTimeGetMcuTime().Seconds;
    tx_pending = true;
    failed_uplinks = 0U;
    /* The modem took the block: the next one starts from here. */
    if (has_block) CommitBlock(&block);
    fault_frame_due = true;
    if (installing)
    {
      Led_Flash(LED_1, 1U, 50U, 0U);
      install_uplinks++;
      if (install_uplinks % INSTALL_LINKCHECK_EVERY == 0U && install_checks < INSTALL_LINKCHECK_MAX)
        install_check_due = true;
    }
  }
  else
  {
    if (tx_failures != UINT16_MAX) tx_failures++;
    /* Duty-cycle backpressure (BUSY/NO_TIME) is expected and not reported. */
    if (tx_status != SMTC_MODEM_RC_BUSY && tx_status != SMTC_MODEM_RC_NO_TIME)
    {
      if (tx_rejected != UINT16_MAX) tx_rejected++;
      Fault_Count(FAULT_CODE(FAULT_CAT_RADIO, FAULT_RADIO_TX_REJECTED));
    }
    /* Duty-cycle and scheduling backpressure are expected, not a crash. */
    if (tx_status != SMTC_MODEM_RC_BUSY && tx_status != SMTC_MODEM_RC_NO_TIME &&
        ++failed_uplinks >= 5U) Runtime_Fault(RUNTIME_FAULT_MODEM);
  }

  if (EventType == TX_ON_TIMER) ScheduleNextRound();
  /* USER CODE END SendTxData_1 */
}

/* Alarm for the next round, from now, plus the pre-measurements it needs.
 * Also used when a downlink changes the interval, so it applies at once. */
/* ADD YOUR SENSOR (slow parts): a sensor that needs seconds to measure gets
 * a pre-measurement timer here like the SCD41/SPS30. Its callback only posts
 * an event; the I2C work runs in ProcessSensorEvents(). */
static void ScheduleNextRound(void)
{
  smtc_modem_status_mask_t status_mask = 0;
  smtc_modem_get_status(STACK_ID, &status_mask);
  uint32_t dutycycle = (CertMode || ((status_mask & SMTC_MODEM_STATUS_JOINED) != SMTC_MODEM_STATUS_JOINED)) ? CERT_TX_DUTYCYCLE : tx_dutycycle_s;

  dutycycle = PowerPolicy_Interval(power_policy.mode, dutycycle);
  bool installing = Installing() && (status_mask & SMTC_MODEM_STATUS_JOINED);
  if (installing) dutycycle = INSTALL_INTERVAL_S;
  if (smtc_modem_alarm_start_timer(dutycycle) != SMTC_MODEM_RC_OK)
    Runtime_Fault(RUNTIME_FAULT_MODEM);
  Runtime_ExpectProgress(dutycycle + 600U);
  next_measurement_at = SysTimeGetMcuTime().Seconds + dutycycle;

  /* Schedule pre-measurement only for the next cycle where data is needed:
   * SCD41 12 s and SPS30 16.5 s ahead, per the plan of the current mode. */
  uint8_t next_counter = (uint8_t)((tx_counter % POWER_ROUNDS) + 1U);
  uint8_t next = installing ? 0U : PowerPolicy_Measurements(power_policy.mode, next_counter);
  planned_mode = power_policy.mode;
  UTIL_TIMER_Stop(&Scd41Timer);
  UTIL_TIMER_Stop(&Scd41RestartTimer);
  UTIL_TIMER_Stop(&Sps30Timer);

  if (SCD41_ENABLED && (next & POWER_MEASURE_CO2))
  {
    UTIL_TIMER_SetPeriod(&Scd41Timer, (dutycycle * 1000U > SCD41_PRE_MEASUREMENT_TIME_MS) ? dutycycle * 1000U - SCD41_PRE_MEASUREMENT_TIME_MS : 1U);
    UTIL_TIMER_Start(&Scd41Timer);
    UTIL_TIMER_SetPeriod(&Scd41RestartTimer, (dutycycle * 1000U > SCD41_RESTART_TIME_MS) ? dutycycle * 1000U - SCD41_RESTART_TIME_MS : 1U);
    UTIL_TIMER_Start(&Scd41RestartTimer);
  }

  if (next & POWER_MEASURE_PM)
  {
    UTIL_TIMER_SetPeriod(&Sps30Timer, (dutycycle * 1000U > SPS30_PRE_MEASUREMENT_TIME_MS) ? dutycycle * 1000U - SPS30_PRE_MEASUREMENT_TIME_MS : 1U);
    UTIL_TIMER_Start(&Sps30Timer);
  }
}

static void processRxData(const uint8_t *payload, uint8_t size, const smtc_modem_dl_metadata_t *metadata)
{
  if ((payload == NULL) || (metadata == NULL))
  {
    APP_LOG(TS_ON, VLEVEL_M, "Ignoring downlink: invalid arguments\r\n");
    return;
  }

  if (size == 0U)
  {
    APP_LOG(TS_ON, VLEVEL_M, "Ignoring downlink: payload size is zero\r\n");
    return;
  }

  if (metadata->fport != RX_CMD_PORT)
  {
    APP_LOG(TS_ON, VLEVEL_M, "Ignoring downlink command on unexpected port %u\r\n", metadata->fport);
    return;
  }

  const uint8_t command = payload[0];
  uint16_t result = FAULT_CMD_OK;
  APP_LOG(TS_ON, VLEVEL_M, "Received command 0x%02X (size=%u, port=%u)\r\n",
          (unsigned)command,
          (unsigned)size,
          metadata->fport);

  switch (command)
  {
    case RX_CMD_TRIGGER_SPS30_CLEANING:
    {
      ReadBattery();
      if (power_policy.mode != POWER_NORMAL || !(battery_sample.valid & SENSOR_VALID_BATTERY))
      {
        result = FAULT_CMD_REFUSED;
        break;
      }
      bool measurement_started = false;
      bool cleaning_started = false;

      APP_LOG(TS_ON, VLEVEL_M, "Message: Trigger SPS30 fan cleaning\r\n");

      if (SPS30_AcquireBus() != SPS30_STATUS_OK)
      {
        APP_LOG(TS_ON, VLEVEL_M, "SPS30 bus acquire failed\r\n");
        result = FAULT_CMD_FAILED;
        break;
      }

      if (SPS30_WakeUp() != SPS30_STATUS_OK)
      {
        (void)SPS30_ReleaseBus();
        APP_LOG(TS_ON, VLEVEL_M, "SPS30 wake-up failed\r\n");
        result = FAULT_CMD_FAILED;
        break;
      }

      if (SPS30_StartMeasurement() == SPS30_STATUS_OK)
      {
        measurement_started = true;
        HAL_Delay(50);
      }
      else
      {
        APP_LOG(TS_ON, VLEVEL_M, "SPS30 start measurement failed\r\n");
      }

      if (measurement_started && (SPS30_StartFanCleaning() == SPS30_STATUS_OK))
      {
        UTIL_TIMER_Start(&Sps30CleanupTimer);
        cleaning_started = true;
        last_sps30_clean_timestamp = SysTimeGetMcuTime().Seconds;
        APP_LOG(TS_ON, VLEVEL_M, "SPS30 fan cleaning started\r\n");
      }
      else if (measurement_started)
      {
        APP_LOG(TS_ON, VLEVEL_M, "SPS30 fan cleaning start failed\r\n");
      }

      if ((cleaning_started == false) && (measurement_started == true))
      {
        (void)SPS30_StopMeasurement();
        (void)SPS30_Sleep();
      }

      (void)SPS30_ReleaseBus();
      if (!cleaning_started) result = FAULT_CMD_FAILED;
      break;
    }
    case RX_CMD_SET_TX_INTERVAL:
    {
      if (size < 3U)
      {
        APP_LOG(TS_ON, VLEVEL_M, "SET_TX_INTERVAL: payload too short (size=%u)\r\n", (unsigned)size);
        result = FAULT_CMD_INVALID;
        break;
      }

      uint16_t new_interval = (uint16_t)(((uint16_t)payload[1] << 8) | (uint16_t)payload[2]);

      if ((new_interval < APP_TX_DUTYCYCLE_MIN_S) || (new_interval > APP_TX_DUTYCYCLE_MAX_S))
      {
        APP_LOG(TS_ON, VLEVEL_M, "SET_TX_INTERVAL: %u s out of range [%u..%u], ignored\r\n",
                (unsigned)new_interval, (unsigned)APP_TX_DUTYCYCLE_MIN_S, (unsigned)APP_TX_DUTYCYCLE_MAX_S);
        result = FAULT_CMD_INVALID;
        break;
      }

      device_settings_t next = settings;
      next.interval_s = new_interval;
      if (Settings_Save(&next))
      {
        /* Applies now, not after the next restart: the next round is
         * rescheduled from this moment with the new interval. */
        Settings_Apply(&next);
        APP_LOG(TS_ON, VLEVEL_M, "SET_TX_INTERVAL: TX interval set to %u s (saved)\r\n", (unsigned)tx_dutycycle_s);
      }
      else
      {
        APP_LOG(TS_ON, VLEVEL_M, "SET_TX_INTERVAL: TX interval unchanged at %u s (flash save FAILED)\r\n", (unsigned)tx_dutycycle_s);
        result = FAULT_CMD_SAVE_FAILED;
      }
      break;
    }
    case SETTINGS_CMD:
    {
      device_settings_t next;
      if (!DeviceSettings_ParseDownlink(payload, size, &next))
      {
        APP_LOG(TS_ON, VLEVEL_M, "SETTINGS: invalid (size=%u), nothing changed\r\n", (unsigned)size);
        result = FAULT_CMD_INVALID;
      }
      else if (!Settings_Save(&next))
      {
        APP_LOG(TS_ON, VLEVEL_M, "SETTINGS: flash save FAILED, nothing changed\r\n");
        result = FAULT_CMD_SAVE_FAILED;
      }
      else
      {
        Settings_Apply(&next);
        APP_LOG(TS_ON, VLEVEL_M, "SETTINGS: revision %u, interval %u s, save %u, recovery %u, standby %u, resume %u mV\r\n",
                (unsigned)next.revision, (unsigned)next.interval_s, (unsigned)next.th.save,
                (unsigned)next.th.recovery, (unsigned)next.th.standby, (unsigned)next.th.resume);
      }
      break;
    }
    case 0x12U:
    {
      uint8_t diagnostic[26] = {1U, (uint8_t)power_policy.mode};
      uint8_t n = 2U;
      uint32_t words[] = {SysTimeGetMcuTime().Seconds, Runtime_BootCount(), Runtime_ResetFlags()};
      for (uint8_t i = 0; i < 3U; ++i)
      { append_u16_be(diagnostic, &n, (uint16_t)(words[i] >> 16)); append_u16_be(diagnostic, &n, (uint16_t)words[i]); }
      append_u16_be(diagnostic, &n, (uint16_t)((Runtime_LastFault() << 8) | Runtime_LastFaultDetail()));
      append_u16_be(diagnostic, &n, tx_failures);
      append_u16_be(diagnostic, &n, sensor_failures);
      append_u16_be(diagnostic, &n, last_valid_sensors);
      append_u16_be(diagnostic, &n, Runtime_PanicCount());
      diagnostic[n++] = Runtime_NvmErrorCount();
      diagnostic[n++] = Runtime_LastNvmError();
      if (smtc_modem_request_uplink(STACK_ID, 5U, false, diagnostic, n) != SMTC_MODEM_RC_OK)
        result = FAULT_CMD_NOT_ACCEPTED;
      break;
    }
    case RX_CMD_SOFTWARE_RESET:
      APP_LOG(TS_ON, VLEVEL_M, "Message: Trigger software reset\r\n");
      /* An acknowledgement queued now would die with the reset: the boot
       * entry 0x0540 carries reason 7 instead. */
      Runtime_Restart(RUNTIME_REASON_COMMAND);
      break;
    default:
      APP_LOG(TS_ON, VLEVEL_M, "Message: Unknown command 0x%02X\r\n", (unsigned)command);
      result = FAULT_CMD_UNKNOWN;
      break;
  }
  /* Leaves with the next fPort 99 frame, not at once. */
  Fault_Event(FAULT_CODE(FAULT_CAT_COMMAND, command), result);
  /* Accepted or refused, the backend gets the values that are in effect. */
  if (command == SETTINGS_CMD || command == RX_CMD_SET_TX_INTERVAL) settings_report_due = true;
}


/* USER CODE BEGIN PrFD_LedEvents */
/*static bool IsAllZero(const uint8_t *buffer, uint8_t size)
{
  for (uint8_t i = 0; i < size; i++)
  {
    if (buffer[i] != 0U)
    {
      return false;
    }
  }

  return true;
}*/

//static void OnTxTimerLedEvent(void *context)
//{
  // HAL_GPIO_WritePin(LED2_GPIO_Port, LED2_Pin, GPIO_PIN_RESET); /* LED_GREEN */
//}

//static void OnRxTimerLedEvent(void *context)
//{
  //HAL_GPIO_WritePin(LED1_GPIO_Port, LED1_Pin, GPIO_PIN_RESET); /* LED_BLUE */
//}

//static void OnJoinTimerLedEvent(void *context)
//{
  // HAL_GPIO_TogglePin(LED3_GPIO_Port, LED3_Pin); /* LED_RED */
//}

static void OnScd41TimerEvent(void *context)
{
  (void)context;
  sensor_events |= EVENT_SCD_START;
}

static void OnScd41RestartTimerEvent(void *context)
{
  (void)context;
  sensor_events |= EVENT_SCD_RESTART;
}

static void OnSps30TimerEvent(void *context)
{
  (void)context;
  sensor_events |= EVENT_SPS_START;
}

static void OnSps30CleanupTimerEvent(void *context)
{
  (void)context;
  sensor_events |= EVENT_SPS_STOP;
}

static void OnSolarTimerEvent(void *context)
{
  (void)context;
  sensor_events |= EVENT_SOLAR;
}

static void SampleSolar(void)
{
  solar_sample_t sample = { 0 };
  INA226_Data_t ina;

  if (INA226_Measure(&ina) == INA226_OK)
  {
    sample.ina_valid = true;
    sample.bus_mv = ina.bus_mv;
    sample.current_01ma = ina.current_01ma;
    Fault_ComponentResult(FAULT_COMP_INA226, true, 0U);
  }
  else
  {
    Fault_ComponentResult(FAULT_COMP_INA226, false, INA226_LastI2cError());
    /* A part missing at boot is retried here, cheaply, every sample; the
     * bus is recovered once, when a read error becomes persistent. */
    if (INA226_Init() != INA226_OK && Fault_IsActive(FAULT_CODE(FAULT_CAT_READ_ERROR, FAULT_COMP_INA226)) &&
        !solar_bus_recovered)
    {
      solar_bus_recovered = true;
      (void)I2C2_RecoverBus();
    }
  }
  if (sample.ina_valid) solar_bus_recovered = false;
  /* The divider is measured as well, also as a cross-check of VBUS. */
  sample.adc_valid = SYS_ReadSolarMv(&sample.adc_mv);
  Fault_ComponentResult(FAULT_COMP_SOLAR_ADC, sample.adc_valid, 0U);
  Solar_Add(&solar_acc, &sample);
}

static void ChargerSafetyTimerReset(void)
{
  BQ25185_ChargeDisable();
  UTIL_TIMER_Start(&ChargerCeTimer);
}

static void OnChargerCeTimerEvent(void *context)
{
  BQ25185_ChargeEnable();
}

static void OnChargerSafetyTimerEvent(void *context)
{
  ChargerSafetyTimerReset();
}

static void Settings_Load(void)
{
  app_store_t store;

  DeviceSettings_Defaults(&settings, APP_TX_DUTYCYCLE);
  settings_from_nvm = false;
  if (Nvm_Read(NVM_CONFIG_OFFSET, &store, sizeof store))
  {
    settings_load_t loaded = DeviceSettings_DecodeRecord(store.settings, &settings);
    settings_from_nvm = loaded == SETTINGS_LOADED;
    /* A broken record means defaults, reported as 0x0543 detail NVM_ERR_SETTINGS. */
    if (loaded == SETTINGS_CORRUPT) Runtime_NoteNvmError(NVM_ERR_SETTINGS);
    /* Nothing usable from 2.1: keep the interval firmware 2.0 stored. */
    if (!settings_from_nvm && store.legacy.magic == APP_CONFIG_MAGIC &&
        DeviceSettings_IntervalValid(store.legacy.tx_dutycycle_s))
      settings.interval_s = (uint16_t)store.legacy.tx_dutycycle_s;
  }
  tx_dutycycle_s = settings.interval_s;
  APP_LOG(TS_OFF, VLEVEL_M, "Settings: revision %u, interval %u s%s\r\n", (unsigned)settings.revision,
          (unsigned)settings.interval_s, settings_from_nvm ? "" : " (defaults)");
}

static bool Settings_Save(const device_settings_t *next)
{
  app_store_t store = { .legacy = { APP_CONFIG_MAGIC, next->interval_s } };
  DeviceSettings_EncodeRecord(next, store.settings);
  /* Nvm_Write skips the flash when nothing changed. */
  return Nvm_Write(NVM_CONFIG_OFFSET, &store, sizeof store);
}

static void Settings_Apply(const device_settings_t *next)
{
  settings = *next;
  settings_from_nvm = true;
  tx_dutycycle_s = settings.interval_s;
  PowerPolicy_SetThresholds(&power_policy, &settings.th);
  if (EventType == TX_ON_TIMER) ScheduleNextRound();
}

/* USER CODE END PrFD_LedEvents */

#if defined (LOW_POWER_DISABLE) && (LOW_POWER_DISABLE == 0)
static void OnSleepTimerEvent(void *context)
{
  APP_LOG(TS_ON, VLEVEL_H, "Sleep timer\r\n");

}
#endif /*(LOW_POWER_DISABLE) && (LOW_POWER_DISABLE == 0) */

/* --- EOF ------------------------------------------------------------------ */
