TexhFexLabs/HydroNodeStation/stm32_node/Core/Inc/sys_conf.h

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

/* Define to prevent recursive inclusion -------------------------------------*/
#ifndef __SYS_CONF_H__
#define __SYS_CONF_H__

#ifdef __cplusplus
extern "C" {
#endif

/* Includes ------------------------------------------------------------------*/
/* Exported types ------------------------------------------------------------*/
/* Exported constants --------------------------------------------------------*/

/**
  * @brief Temperature and pressure values are retrieved from sensors shield
  *        (instead of sending dummy values). It requires MEMS IKS shield
  */
#define SENSOR_ENABLED                       0

/**
  * @brief  Verbose level for all trace logs
  */
#define VERBOSE_LEVEL                        VLEVEL_M

/**
  * @brief Enable trace logs
  */
#ifndef APP_LOG_ENABLED
#define APP_LOG_ENABLED                      0
#endif

/**
  * @brief Activate monitoring (probes) of some internal RF signals for debug purpose
  */
#define DEBUG_SUBGHZSPI_MONITORING_ENABLED   0

#define DEBUG_RF_NRESET_ENABLED              0

#define DEBUG_RF_HSE32RDY_ENABLED            0

#define DEBUG_RF_SMPSRDY_ENABLED             0

#define DEBUG_RF_LDORDY_ENABLED              0

#define DEBUG_RF_DTB1_ENABLED                0

#define DEBUG_RF_BUSY_ENABLED                0

/**
  * @brief Enable/Disable MCU Debugger pins (dbg serial wires)
  * @note  by HW serial wires are ON by default, need to put them OFF to save power
  */
#define DEBUGGER_ENABLED                     0

/**
  * @brief Disable Low Power mode
  * @note  0: LowPowerMode enabled. MCU enters stop2 mode, 1: LowPowerMode disabled. MCU enters sleep mode only
  */
#define LOW_POWER_DISABLE                    0

/* USER CODE BEGIN EC */

/* SCD41 sensor support -----------------------------------------------------*/
/**
  * @brief Contact counters on P4 (PA4 rain, PA5 wind). Off by default: the
  *        pins stay analog and the block reports 0xFFFF for both counters.
  */
#ifndef PULSE_COUNTERS_ENABLED
#define PULSE_COUNTERS_ENABLED             0
#endif

#ifndef SCD41_ENABLED
#define SCD41_ENABLED                      1
#endif

/* I2C2 bus configuration is generated by CubeMX in Core/Src/i2c.c */
#define SCD41_I2C_TIMEOUT_MS               100U

/* Single-shot timing from SCD41 datasheet */
#define SCD41_WAKEUP_DELAY_MS              30U
#define SCD41_SINGLE_SHOT_WAIT_MS          5000U
#define SCD41_SINGLE_SHOT_RHT_WAIT_MS      50U

/* SCD41 runtime configuration */
#define SCD41_TEMPERATURE_OFFSET_C_X100    0U
#define SCD41_SENSOR_ALTITUDE_M            0U
#define SCD41_AMBIENT_PRESSURE_MBAR        0U
#define SCD41_ASC_ENABLED                  0U
#define SCD41_PERSIST_SETTINGS             0U

/* USER CODE END EC */

/* External variables --------------------------------------------------------*/
/* Exported macro ------------------------------------------------------------*/
/* Exported functions prototypes ---------------------------------------------*/
#ifdef __cplusplus
}
#endif

#endif /* __SYS_CONF_H__ */
