TexhFexLabs/HydroNodeStation/stm32_node/Core/Src/usart_if.c

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

/* Includes ------------------------------------------------------------------*/
#include "usart_if.h"
#include <stdbool.h>

/* USER CODE BEGIN Includes */
#include "usart.h"

/* USER CODE END Includes */

/* External variables ---------------------------------------------------------*/
/**
  * @brief UART handle
  */
extern UART_HandleTypeDef huart1;

/**
  * @brief buffer to receive 1 character
  */
uint8_t charRx;

/**
  * @brief Trace driver callbacks handler
  */
const UTIL_ADV_TRACE_Driver_s UTIL_TraceDriver =
{
  vcom_Init,
  vcom_DeInit,
  vcom_ReceiveInit,
  vcom_Trace_DMA,
};

/**
  * @brief  TX complete callback
  * @return none
  */
static void (*TxCpltCallback)(void *);
/**
  * @brief  RX complete callback
  * @param  rxChar ptr of chars buffer sent by user
  * @param  size buffer size
  * @param  error errorcode
  * @return none
  */
static void (*RxCpltCallback)(uint8_t *rxChar, uint16_t size, uint8_t error);

/* USER CODE BEGIN PV */
/**
  * @brief USART1 is clocked and its pins are in AF mode
  */
static bool debug_uart_on;
/* USER CODE END PV */


/* Exported functions --------------------------------------------------------*/

UTIL_ADV_TRACE_Status_t vcom_Init(void (*cb)(void *))
{
  TxCpltCallback = cb;
#if APP_LOG_ENABLED
  DebugUart_Start();
#endif
  return UTIL_ADV_TRACE_OK;
}

UTIL_ADV_TRACE_Status_t vcom_DeInit(void)
{
  /* ##-1- Reset peripherals ################################################## */
  __HAL_RCC_USART1_FORCE_RESET();
  __HAL_RCC_USART1_RELEASE_RESET();

  /* ##-2- MspDeInit ################################################## */
  HAL_UART_MspDeInit(&huart1);

  /* ##-3- Disable the NVIC for DMA ########################################### */
  /* USER CODE BEGIN 1 */
  HAL_NVIC_DisableIRQ(DMA1_Channel5_IRQn);

  return UTIL_ADV_TRACE_OK;
  /* USER CODE END 1 */
}

void vcom_Trace(uint8_t *p_data, uint16_t size)
{
  DebugUart_WriteBytes(p_data, size);
}

UTIL_ADV_TRACE_Status_t vcom_Trace_DMA(uint8_t *p_data, uint16_t size)
{
  vcom_Trace(p_data, size);
  if (TxCpltCallback != NULL)
  {
    TxCpltCallback(NULL);
  }
  return UTIL_ADV_TRACE_OK;
}

UTIL_ADV_TRACE_Status_t vcom_ReceiveInit(void (*RxCb)(uint8_t *rxChar, uint16_t size, uint8_t error))
{
  RxCpltCallback = RxCb;

  return UTIL_ADV_TRACE_OK;
}

void vcom_Resume(void)
{
  /* USART1 loses its configuration in STOP2: restart it if it was running. */
  if (debug_uart_on)
  {
    debug_uart_on = false;
    DebugUart_Start();
  }
}

void HAL_UART_TxCpltCallback(UART_HandleTypeDef *huart)
{
  /* buffer transmission complete*/
  if (huart->Instance == USART1)
  {
    TxCpltCallback(NULL);
  }
}

void HAL_UART_RxCpltCallback(UART_HandleTypeDef *huart)
{
  if (huart->Instance == USART1)
  {
    if ((NULL != RxCpltCallback) && (HAL_UART_ERROR_NONE == huart->ErrorCode))
    {
      RxCpltCallback(&charRx, 1, 0);
    }
    HAL_UART_Receive_IT(huart, &charRx, 1);
  }
}

/* USER CODE BEGIN EF */

/* USART1 on H1 (PB6 TX, PB7 RX), 115200 8N1. Started only while something
 * is printed (Debug build trace or the DIP 3 debug profile); otherwise the
 * peripheral stays unclocked and PB6/PB7 stay analog. Present in every
 * build, unlike APP_LOG. */
void DebugUart_Start(void)
{
  if (debug_uart_on) return;
  MX_USART1_UART_Init();
  debug_uart_on = true;
}

void DebugUart_Stop(void)
{
  if (!debug_uart_on) return;
  (void)HAL_UART_DeInit(&huart1);
  debug_uart_on = false;
}

void DebugUart_WriteBytes(const uint8_t *data, uint16_t size)
{
  if (!debug_uart_on || size == 0U) return;
  /* About 87 us per byte at 115200 Bd; allow twice that plus a margin. */
  (void)HAL_UART_Transmit(&huart1, data, size, 10U + (uint32_t)size / 5U);
}

void DebugUart_Write(const char *s)
{
  uint16_t n = 0U;
  while (s[n] != '\0' && n < UINT16_MAX) n++;
  DebugUart_WriteBytes((const uint8_t *)s, n);
}

int __io_putchar(int ch)
{
  uint8_t c = (uint8_t)ch;
  DebugUart_WriteBytes(&c, 1U);
  return ch;
}

/* USER CODE END EF */
