TexhFexLabs/HydroNodeStation/stm32_node/Core/Src/i2c.c

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
/* Includes ------------------------------------------------------------------*/
#include "i2c.h"
#include "fault_report.h"

#include "sys_app.h"

/* USER CODE BEGIN 0 */
/**
 * @brief  I2C Bus Recovery: Toggles SCL 9 times to free a stuck SDA line.
 */
int32_t I2C2_RecoverBus(void)
{
  GPIO_InitTypeDef GPIO_InitStruct = {0};

  /* 1. De-initialize I2C2 */
  HAL_I2C_DeInit(&hi2c2);

  /* 2. Configure SCL and SDA as GPIO Outputs */
  __HAL_RCC_GPIOA_CLK_ENABLE();
  __HAL_RCC_GPIOB_CLK_ENABLE();

  /* PA11: SDA, PA12: SCL */
  GPIO_InitStruct.Pin = GPIO_PIN_11;
  GPIO_InitStruct.Mode = GPIO_MODE_OUTPUT_OD;
  GPIO_InitStruct.Pull = GPIO_PULLUP;
  GPIO_InitStruct.Speed = GPIO_SPEED_FREQ_LOW;
  HAL_GPIO_Init(GPIOA, &GPIO_InitStruct); /* SDA */

  GPIO_InitStruct.Pin = GPIO_PIN_12;
  HAL_GPIO_Init(GPIOA, &GPIO_InitStruct); /* SCL */

  /* 3. Toggle SCL 9 times */
  HAL_GPIO_WritePin(GPIOA, GPIO_PIN_11, GPIO_PIN_SET); /* SDA high */
  for (int i = 0; i < 9; i++)
  {
    HAL_GPIO_WritePin(GPIOA, GPIO_PIN_12, GPIO_PIN_RESET);
    HAL_Delay(1);
    HAL_GPIO_WritePin(GPIOA, GPIO_PIN_12, GPIO_PIN_SET);
    HAL_Delay(1);
  }

  /* 4. Generate a STOP condition manually */
  HAL_GPIO_WritePin(GPIOA, GPIO_PIN_11, GPIO_PIN_RESET);
  HAL_Delay(1);
  HAL_GPIO_WritePin(GPIOA, GPIO_PIN_12, GPIO_PIN_SET);
  HAL_Delay(1);
  HAL_GPIO_WritePin(GPIOA, GPIO_PIN_11, GPIO_PIN_SET);
  HAL_Delay(1);

  /* 5. Re-initialize I2C2 */
  uint8_t released = HAL_GPIO_ReadPin(GPIOA, GPIO_PIN_11) == GPIO_PIN_SET &&
                     HAL_GPIO_ReadPin(GPIOA, GPIO_PIN_12) == GPIO_PIN_SET;
  MX_I2C2_Init();
  /* Three failed recoveries in a row are reported as 0x0210 on fPort 99. */
  Fault_ComponentResult(FAULT_COMP_I2C_BUS, released != 0U, 0U);
  return released ? 0 : -1;
}
/* USER CODE END 0 */

I2C_HandleTypeDef hi2c2;

/* I2C2 init function */
void MX_I2C2_Init(void)
{

  hi2c2.Instance = I2C2;
  hi2c2.Init.Timing = 0x10805D88;
  hi2c2.Init.OwnAddress1 = 0;
  hi2c2.Init.AddressingMode = I2C_ADDRESSINGMODE_7BIT;
  hi2c2.Init.DualAddressMode = I2C_DUALADDRESS_DISABLE;
  hi2c2.Init.OwnAddress2 = 0;
  hi2c2.Init.OwnAddress2Masks = I2C_OA2_NOMASK;
  hi2c2.Init.GeneralCallMode = I2C_GENERALCALL_DISABLE;
  hi2c2.Init.NoStretchMode = I2C_NOSTRETCH_DISABLE;
  if (HAL_I2C_Init(&hi2c2) != HAL_OK)
  {
    APP_LOG(TS_OFF, VLEVEL_M, "I2C2 Init Failed\r\n");
  }

  /** Configure Analogue filter
  */
  if (HAL_I2CEx_ConfigAnalogFilter(&hi2c2, I2C_ANALOGFILTER_ENABLE) != HAL_OK)
  {
    APP_LOG(TS_OFF, VLEVEL_M, "I2C2 Analog Filter Config Failed\r\n");
  }

  /** Configure Digital filter
  */
  if (HAL_I2CEx_ConfigDigitalFilter(&hi2c2, 0) != HAL_OK)
  {
    APP_LOG(TS_OFF, VLEVEL_M, "I2C2 Digital Filter Config Failed\r\n");
  }
}

void HAL_I2C_MspInit(I2C_HandleTypeDef* i2cHandle)
{

  GPIO_InitTypeDef GPIO_InitStruct = {0};
  RCC_PeriphCLKInitTypeDef PeriphClkInitStruct = {0};
  if(i2cHandle->Instance==I2C2)
  {
  /** Initializes the peripherals clocks
  */
    PeriphClkInitStruct.PeriphClockSelection = RCC_PERIPHCLK_I2C2;
    PeriphClkInitStruct.I2c2ClockSelection = RCC_I2C2CLKSOURCE_PCLK1;
    if (HAL_RCCEx_PeriphCLKConfig(&PeriphClkInitStruct) != HAL_OK)
    {
      Error_Handler();
    }

    __HAL_RCC_GPIOA_CLK_ENABLE();
    /**I2C2 GPIO Configuration
    PA11     ------> I2C2_SDA
    PA12     ------> I2C2_SCL
    */
    GPIO_InitStruct.Pin = GPIO_PIN_11;
    GPIO_InitStruct.Mode = GPIO_MODE_AF_OD;
    GPIO_InitStruct.Pull = GPIO_NOPULL;
    GPIO_InitStruct.Speed = GPIO_SPEED_FREQ_LOW;
    GPIO_InitStruct.Alternate = GPIO_AF4_I2C2;
    HAL_GPIO_Init(GPIOA, &GPIO_InitStruct);

    GPIO_InitStruct.Pin = GPIO_PIN_12;
    GPIO_InitStruct.Mode = GPIO_MODE_AF_OD;
    GPIO_InitStruct.Pull = GPIO_NOPULL;
    GPIO_InitStruct.Speed = GPIO_SPEED_FREQ_LOW;
    GPIO_InitStruct.Alternate = GPIO_AF4_I2C2;
    HAL_GPIO_Init(GPIOA, &GPIO_InitStruct);

    /* I2C2 clock enable */
    __HAL_RCC_I2C2_CLK_ENABLE();

    /* I2C2 interrupt Init */
    HAL_NVIC_SetPriority(I2C2_EV_IRQn, 0, 0);
    HAL_NVIC_EnableIRQ(I2C2_EV_IRQn);
    HAL_NVIC_SetPriority(I2C2_ER_IRQn, 0, 0);
    HAL_NVIC_EnableIRQ(I2C2_ER_IRQn);
  }
}

void HAL_I2C_MspDeInit(I2C_HandleTypeDef* i2cHandle)
{

  if(i2cHandle->Instance==I2C2)
  {
    /* Peripheral clock disable */
    __HAL_RCC_I2C2_CLK_DISABLE();

    /**I2C2 GPIO Configuration
    PA11     ------> I2C2_SDA
    PA12     ------> I2C2_SCL
    */
    HAL_GPIO_DeInit(GPIOA, GPIO_PIN_11);
    HAL_GPIO_DeInit(GPIOA, GPIO_PIN_12);

    /* I2C2 interrupt Deinit */
    HAL_NVIC_DisableIRQ(I2C2_EV_IRQn);
    HAL_NVIC_DisableIRQ(I2C2_ER_IRQn);
  }
}
