TexhFexLabs/HydroNodeStation/stm32_node/Core/Src/sys_debug.c

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

/* Includes ------------------------------------------------------------------*/
#include "platform.h"
#include "sys_debug.h"

/* External variables ---------------------------------------------------------*/
/* USER CODE BEGIN PD */
/* RF monitor outputs that would land on pins PCB 1.1 uses. */
#if (DEBUG_RF_NRESET_ENABLED == 1) || (DEBUG_RF_BUSY_ENABLED == 1)
#error "PA11/PA12 are I2C2 on PCB 1.1; RF NRESET/BUSY monitoring is not available"
#endif
#if (DEBUG_SUBGHZSPI_MONITORING_ENABLED == 1) || (DEBUG_RF_SMPSRDY_ENABLED == 1) || \
    (DEBUG_RF_LDORDY_ENABLED == 1) || (DEBUG_RF_DTB1_ENABLED == 1)
#error "PA4..PA7, PB2, PB3 and PB4 are board signals on PCB 1.1; RF monitoring there is not available"
#endif
/* USER CODE END PD */

/* Exported functions --------------------------------------------------------*/

/**
  * @brief Initializes the SW probes pins and the monitor RF pins via Alternate Function
  */
void DBG_Init(void)
{
  /* SW probes */
#if defined (DEBUGGER_ENABLED) && ( DEBUGGER_ENABLED == 0 )
  HAL_DBGMCU_DisableDBGSleepMode();
  HAL_DBGMCU_DisableDBGStopMode();
  HAL_DBGMCU_DisableDBGStandbyMode();
#elif defined (DEBUGGER_ENABLED) && ( DEBUGGER_ENABLED == 1 )
  /*Debug power up request wakeup CBDGPWRUPREQ*/
  LL_EXTI_EnableIT_32_63(LL_EXTI_LINE_46);
  /* Disabled HAL_DBGMCU_  */
  HAL_DBGMCU_EnableDBGSleepMode();
  HAL_DBGMCU_EnableDBGStopMode();
  HAL_DBGMCU_EnableDBGStandbyMode();
#elif !defined (DEBUGGER_ENABLED)
#error "DEBUGGER_ENABLED not defined or out of range <0,1>"
#endif /* DEBUGGER_OFF */

  /* No SW probe pins on PCB 1.1. This function never touches PA11/PA12
   * (I2C2) or PB12 (RF switch supply), with or without DEBUGGER_ENABLED. */
  GPIO_InitTypeDef  GPIO_InitStruct = {0};
  (void)GPIO_InitStruct;

  /* HW alternate functions for monitoring RF */

#if (DEBUG_SUBGHZSPI_MONITORING_ENABLED == 1)
  /*spi dbg*/
  GPIO_InitStruct.Pin    = (GPIO_PIN_4 | GPIO_PIN_5 | GPIO_PIN_6 | GPIO_PIN_7);
  GPIO_InitStruct.Mode   = GPIO_MODE_AF_PP;
  GPIO_InitStruct.Pull   = GPIO_NOPULL;
  GPIO_InitStruct.Speed  = GPIO_SPEED_FREQ_VERY_HIGH;
  GPIO_InitStruct.Alternate  = GPIO_AF13_DEBUG_SUBGHZSPI;
  __HAL_RCC_GPIOA_CLK_ENABLE();
  HAL_GPIO_Init(GPIOA, &GPIO_InitStruct);
#endif /* DEBUG_SUBGHZSPI_MONITORING_ENABLED */


#if (DEBUG_RF_HSE32RDY_ENABLED == 1)
  GPIO_InitStruct.Pin = GPIO_PIN_10;
  GPIO_InitStruct.Mode = GPIO_MODE_AF_PP;
  GPIO_InitStruct.Pull = GPIO_NOPULL;
  GPIO_InitStruct.Speed = GPIO_SPEED_FREQ_VERY_HIGH;
  GPIO_InitStruct.Alternate = GPIO_AF13_DEBUG_RF;
  __HAL_RCC_GPIOA_CLK_ENABLE();
  HAL_GPIO_Init(GPIOA, &GPIO_InitStruct);
#endif /* DEBUG_RF_HSE32RDY_ENABLED */

#if (DEBUG_RF_SMPSRDY_ENABLED == 1)
  GPIO_InitStruct.Pin    = (GPIO_PIN_2);
  GPIO_InitStruct.Mode   = GPIO_MODE_AF_PP;
  GPIO_InitStruct.Pull   = GPIO_NOPULL;
  GPIO_InitStruct.Speed  = GPIO_SPEED_FREQ_VERY_HIGH;
  GPIO_InitStruct.Alternate  = GPIO_AF13_DEBUG_RF;
  __HAL_RCC_GPIOB_CLK_ENABLE();
  HAL_GPIO_Init(GPIOB, &GPIO_InitStruct);
#endif /* DEBUG_RF_SMPSRDY_ENABLED */

#if (DEBUG_RF_LDORDY_ENABLED == 1)
  GPIO_InitStruct.Pin    = (GPIO_PIN_4);
  GPIO_InitStruct.Mode   = GPIO_MODE_AF_PP;
  GPIO_InitStruct.Pull   = GPIO_NOPULL;
  GPIO_InitStruct.Speed  = GPIO_SPEED_FREQ_VERY_HIGH;
  GPIO_InitStruct.Alternate  = GPIO_AF13_DEBUG_RF;
  __HAL_RCC_GPIOB_CLK_ENABLE();
  HAL_GPIO_Init(GPIOB, &GPIO_InitStruct);
#endif /* DEBUG_RF_LDORDY_ENABLED */

#if (DEBUG_RF_DTB1_ENABLED == 1)
  GPIO_InitStruct.Pin = GPIO_PIN_3;
  GPIO_InitStruct.Mode = GPIO_MODE_AF_PP;
  GPIO_InitStruct.Pull = GPIO_NOPULL;
  GPIO_InitStruct.Speed = GPIO_SPEED_FREQ_VERY_HIGH;
  GPIO_InitStruct.Alternate = GPIO_AF13_DEBUG_RF;
  __HAL_RCC_GPIOB_CLK_ENABLE();
  HAL_GPIO_Init(GPIOB, &GPIO_InitStruct);
#endif /* DEBUG_RF_DTB1_ENABLED */


}
