TexhFexLabs/HydroNodeStation/stm32_node/Core/Inc/payload.h

#ifndef PAYLOAD_H
#define PAYLOAD_H
#include <stdint.h>
#include "sys_sensors.h"
/* Uplink layouts of firmware 2.0 (TD_2_0_14). All fields are big-endian
 * 16-bit values; every port always has the same length.
 *   fPort 2: base (10)              + block (22) = 32 bytes
 *   fPort 3: base (10) + CO2 (2)    + block (22) = 34 bytes
 *   fPort 4: base (10) + CO2 + PM (22), no block  = 32 bytes (unchanged)
 * Base: T i16 0.01 degC, RH u16 0.01 %, p u16 0.1 hPa, VBAT u16 mV,
 * UV u16 0.01. Port 4 + block (54 bytes) would not fit DR0-DR2 (51 bytes).
 * Missing values: 0xFFFF (u16) and 0x8000 (i16). */
#define PAYLOAD_PORT_BASE      2U
#define PAYLOAD_PORT_CO2       3U
#define PAYLOAD_PORT_FULL      4U
#define PAYLOAD_BLOCK_LEN      22U
#define PAYLOAD_MAX_LEN        34U

/* "Since the last block" means since the last block the modem accepted;
 * port 4 rounds carry no block, their values flow into the next one. */
typedef struct
{
    uint16_t solar_mv;       /* INA226 mean, mV */
    uint16_t solar_01ma;     /* INA226 mean, 0.1 mA */
    uint16_t solar_mw;       /* mean V x I, mW */
    uint16_t solar_01mwh;    /* energy since last block, 0.1 mWh */
    uint16_t sun_s;          /* sunshine since last block, s */
    uint16_t solar_adc_mv;   /* PB2 divider mean, mV */
    uint16_t soc_x100;       /* MAX17048 SOC, 0.01 % */
    int16_t  crate_x100;     /* MAX17048 charge rate, 0.01 %/h */
    int16_t  board_t_x100;   /* internal sensor, 0.01 degC */
    uint16_t count1;         /* PA4 pulses since last block, 0xFFFF = off */
    uint16_t count2;         /* PA5 pulses since last block, 0xFFFF = off */
} payload_block_t;

/* Port from the sensors read this round: PM -> 4, CO2 -> 3, else 2. */
uint8_t Payload_Port(uint8_t sensor_flags);
/* Writes the frame for port into buf (PAYLOAD_MAX_LEN bytes); returns its
 * length, 0 for an unknown port. block is ignored on port 4. */
uint8_t Payload_Encode(uint8_t port, const sensor_t *s, const payload_block_t *block, uint8_t *buf);
#endif
