TexhFexLabs/HydroNodeStation/stm32_node/Core/Inc/adc_if.h

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

/* Define to prevent recursive inclusion -------------------------------------*/
#ifndef __ADC_IF_H__
#define __ADC_IF_H__

#ifdef __cplusplus
extern "C" {
#endif
/* Includes ------------------------------------------------------------------*/
#include "adc.h"
#include "platform.h"

/* USER CODE BEGIN Includes */
#include <stdbool.h>

/* USER CODE END Includes */

/* Exported types ------------------------------------------------------------*/
/* Exported constants --------------------------------------------------------*/
/**
  * @brief Maximum battery level in mV
  */
#define VDD_BAT                     4250
/**
  * @brief Minimum battery level in mV
  */
#define VDD_MIN                     3200

/* External variables --------------------------------------------------------*/
/* Exported macro ------------------------------------------------------------*/
/* Exported functions prototypes ---------------------------------------------*/

/**
  * @brief  Initializes the ADC input
  */
void SYS_InitMeasurement(void);

/**
  * @brief DeInitializes the ADC
  */
void SYS_DeInitMeasurement(void);

/**
  * @brief  Get the current temperature
  * @return value temperature in degree Celsius( q7.8 )
  */
int16_t SYS_GetTemperatureLevel(void);

/**
  * @brief Get the current battery level
  * @return value battery level in linear scale
  */
uint16_t SYS_GetBatteryLevel(void);

/* USER CODE BEGIN EFP */
/**
  * @brief  Solar panel voltage from the PB2 divider (x2.5), VREFINT-scaled
  * @param  panel_mv voltage in mV
  * @return false on an ADC error (nothing written)
  */
bool SYS_ReadSolarMv(uint16_t *panel_mv);

/**
  * @brief  Internal temperature sensor in 0.01 degC, factory-calibrated
  * @param  temperature_x100 board temperature in 0.01 degC
  * @return false on an ADC error or missing calibration (nothing written)
  */
bool SYS_ReadBoardTemperature(int16_t *temperature_x100);
/* USER CODE END EFP */

#ifdef __cplusplus
}
#endif

#endif /* __ADC_IF_H__ */
